w4rkvs/OG-star-tracker-/mechanics/Pcb box/Bottom part of the box.stl

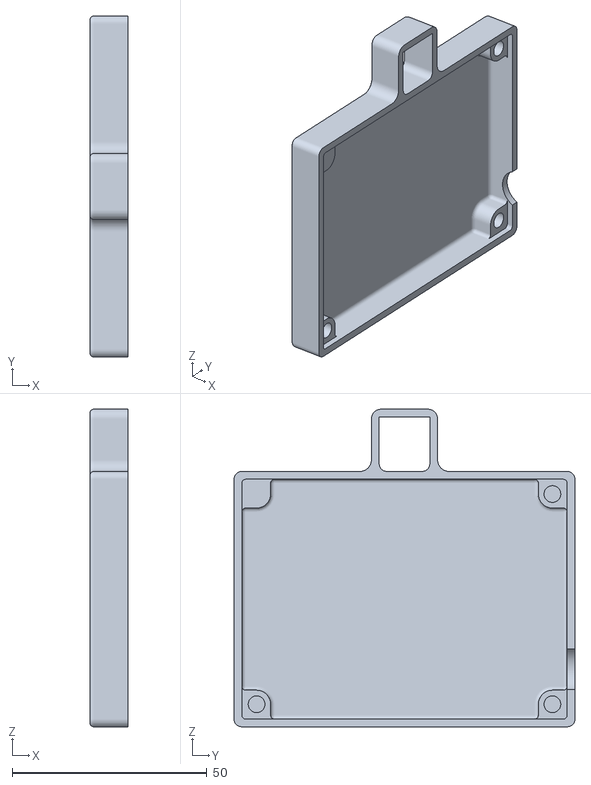
[picture p17: CAD file, 2024-11-18]
mechanics/Pcb box/Bottom part of the box.stl
9.78 x 87.6 x 81.6
