w4rkvs/OG-star-tracker-/mechanics/Test print/test.stl

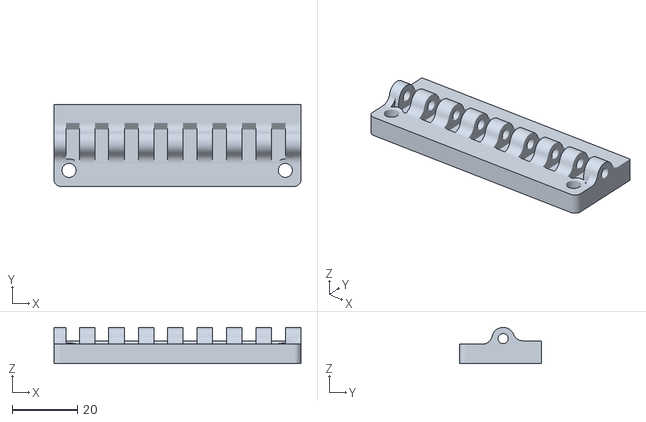
[picture p18: CAD file, 2024-11-18]
mechanics/Test print/test.stl
75.6 x 25.0 x 11.1
