w4rkvs/OG-star-tracker-/mechanics/Top assembly/4 part of geabox.stl

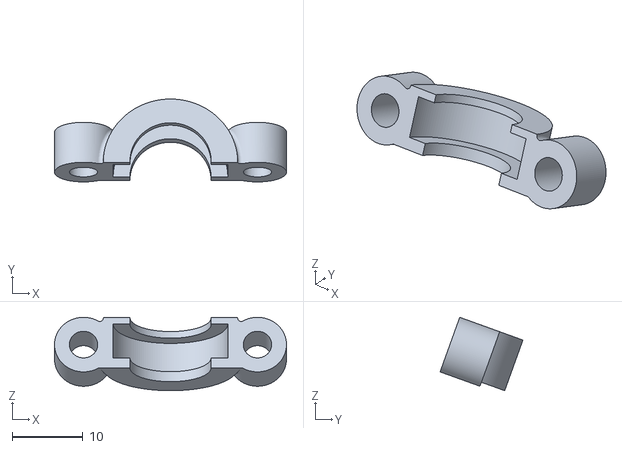
[picture p19: CAD file, 2024-11-18]
mechanics/Top assembly/4 part of geabox.stl
32.8 x 11.7 x 10.4
