w4rkvs/OG-star-tracker-/v1/mechanics/electronic box/top cover.stl

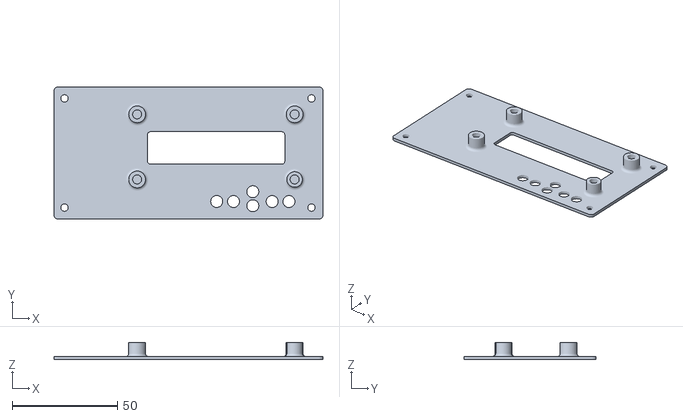
[picture p20: CAD file, 2024-11-18]
v1/mechanics/electronic box/top cover.stl
128.1 x 63.0 x 8.20
