w4rkvs/OG-star-tracker-/v1/mechanics/top asembly/tightener 2x.stl

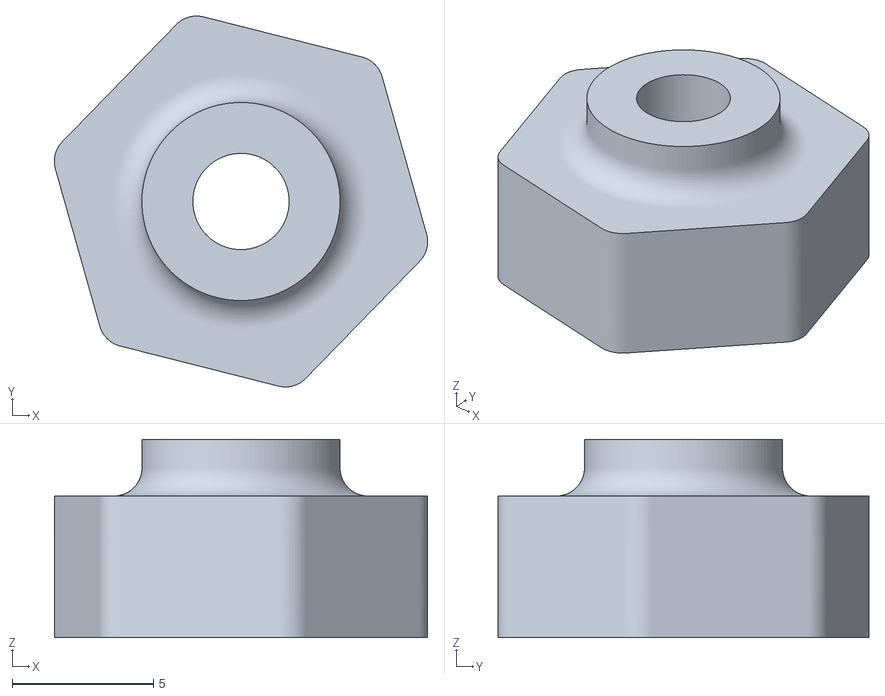
[picture p21: CAD file, 2024-11-18]
v1/mechanics/top asembly/tightener 2x.stl
13.2 x 13.1 x 7.00
