w4rkvs/OG-star-tracker-/v1/mechanics/you also need to print this/bottom holder 2x!.stl

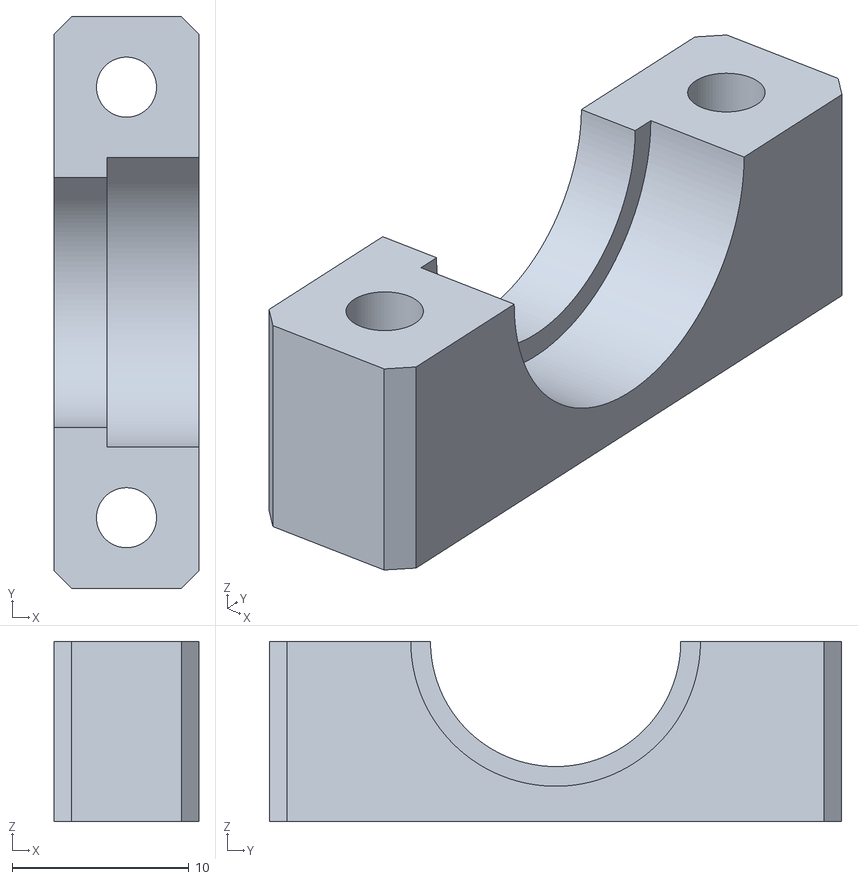
[picture p22: CAD file, 2024-11-18]
v1/mechanics/you also need to print this/bottom holder 2x!.stl
8.20 x 32.4 x 10.2
