w4rkvs/OG-star-tracker-/mechanics/arduino box/box.stl

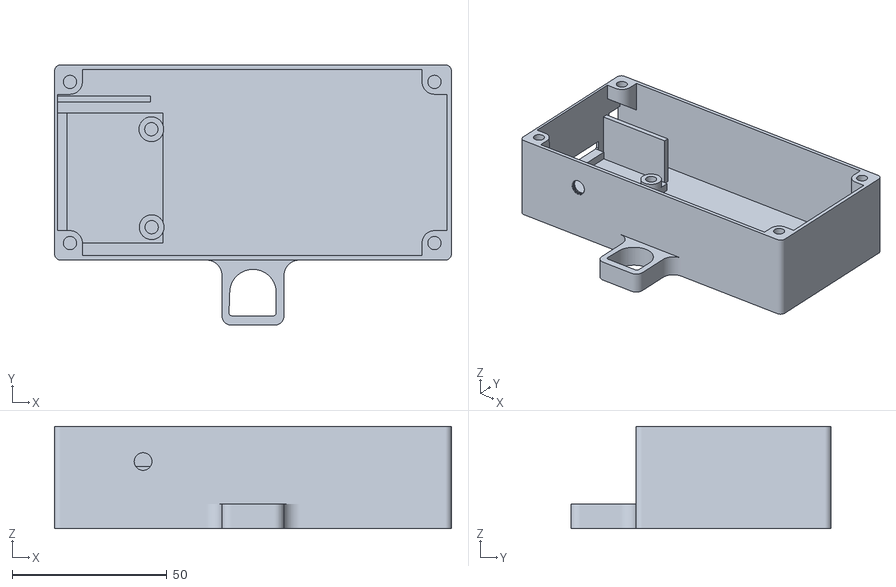
[picture p23: CAD file, 2024-11-18]
mechanics/arduino box/box.stl
128.1 x 84.0 x 33.0
