w4rkvs/OG-star-tracker-/mechanics/DEC upgrade RADEK/bottom-counterweight.stl

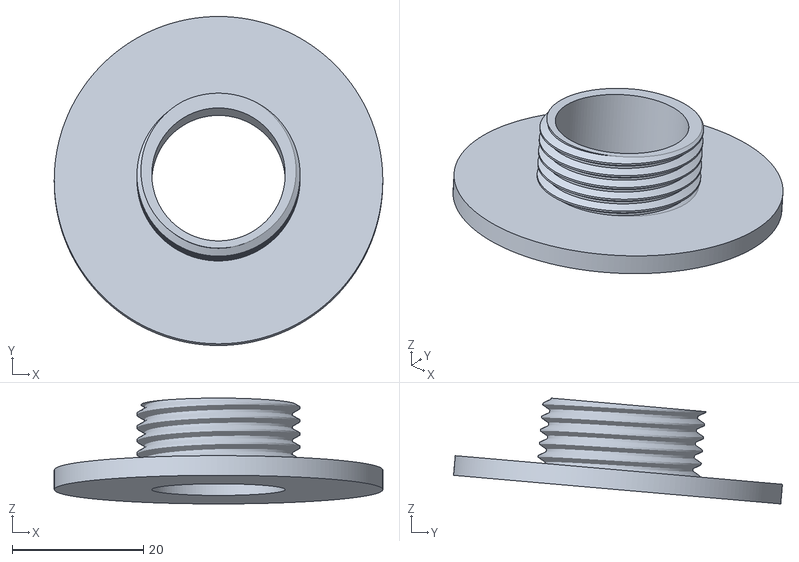
[picture p24: CAD file, 2024-11-18]
mechanics/DEC upgrade RADEK/bottom-counterweight.stl
50.0 x 50.1 x 16.1
