w4rkvs/OG-star-tracker-/mechanics/Knobs and rest of the things/cover for rotating bearing holder.stl

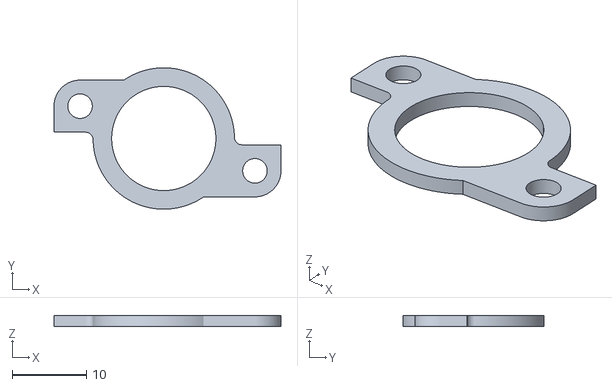
[picture p25: CAD file, 2024-11-18]
mechanics/Knobs and rest of the things/cover for rotating bearing holder.stl
30.5 x 19.0 x 1.50
