w4rkvs/OG-star-tracker-/mechanics/Pcb box/top part.stl

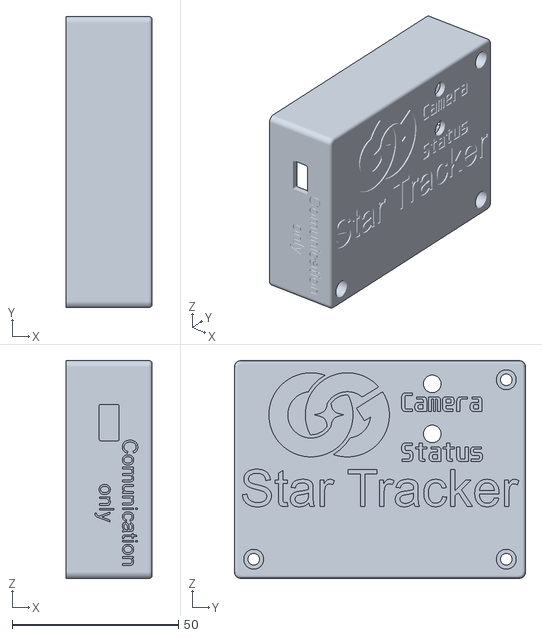
[picture p26: CAD file, 2024-11-18]
mechanics/Pcb box/top part.stl
26.0 x 87.6 x 65.6
