w4rkvs/OG-star-tracker-/mechanics/Test print/test 2.stl

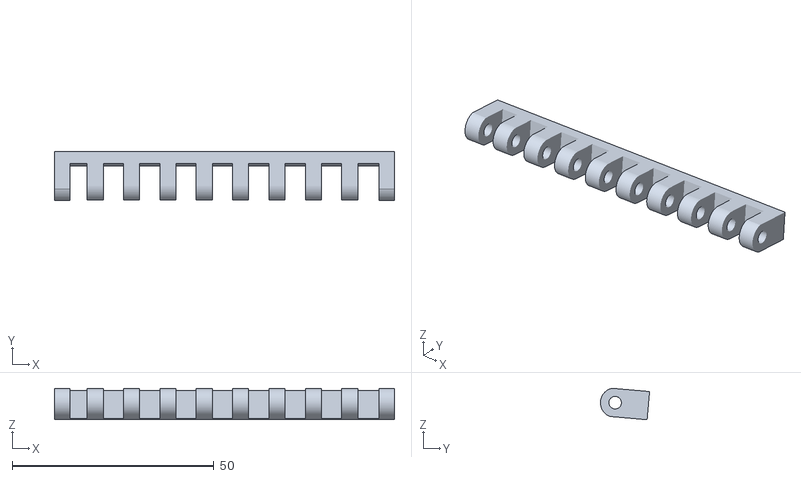
[picture p27: CAD file, 2024-11-18]
mechanics/Test print/test 2.stl
84.2 x 12.2 x 7.79
