w4rkvs/OG-star-tracker-/mechanics/Top assembly/Camera holder m6.stl

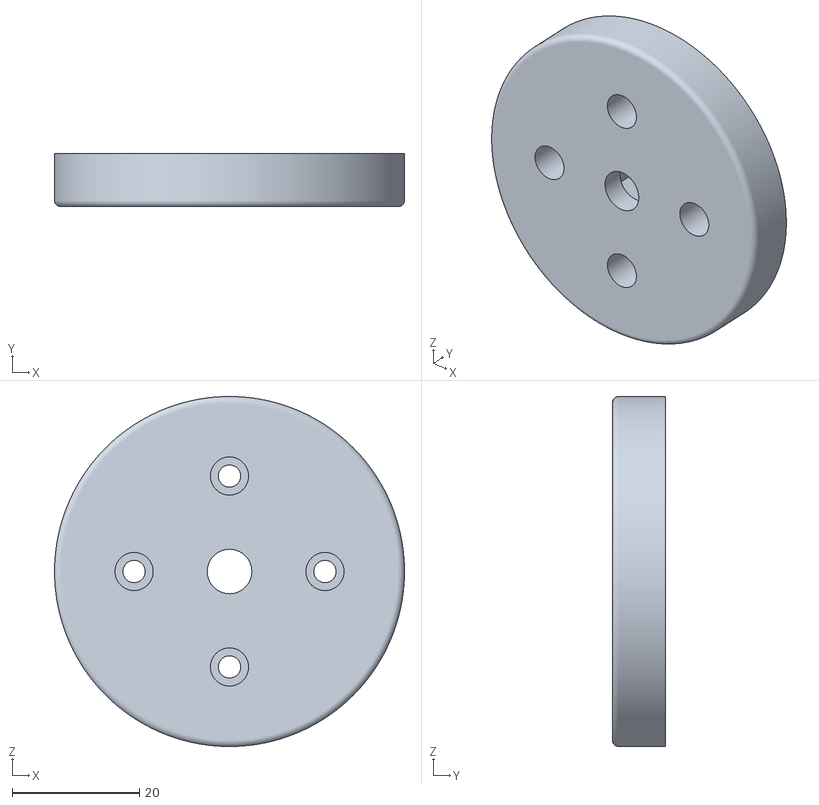
[picture p28: CAD file, 2024-11-18]
mechanics/Top assembly/Camera holder m6.stl
55.0 x 8.40 x 55.0
