w4rkvs/OG-star-tracker-/v1/mechanics/bottom asembly/m5 holder right.stl

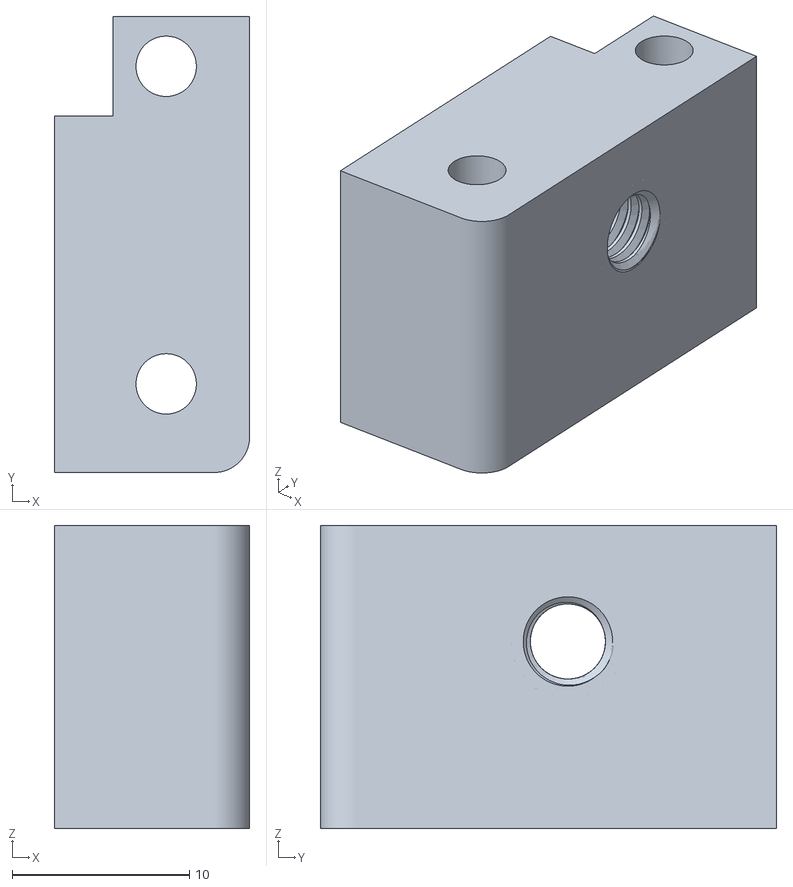
[picture p29: CAD file, 2024-11-18]
v1/mechanics/bottom asembly/m5 holder right.stl
11.0 x 25.7 x 17.1
