w4rkvs/OG-star-tracker-/v1/mechanics/top asembly/gearbox part 2.stl

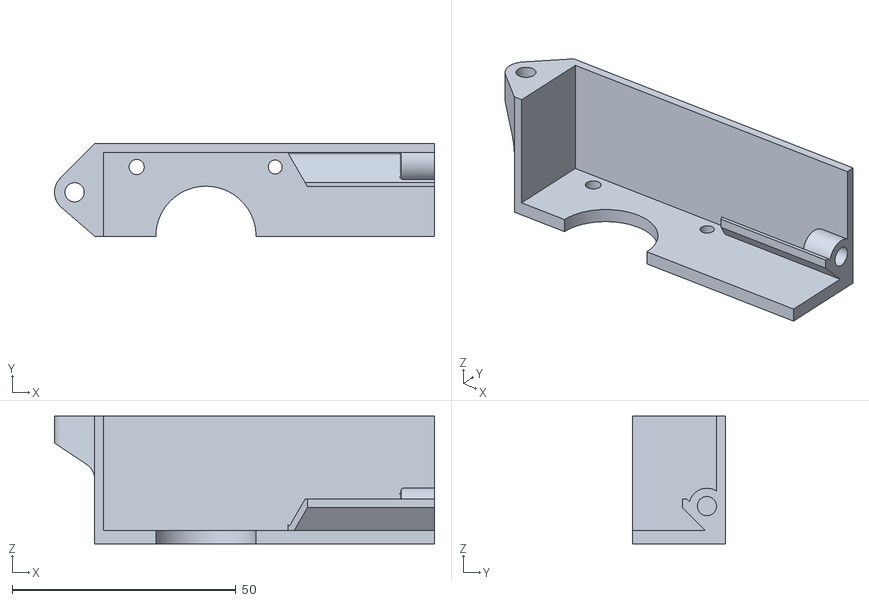
[picture p30: CAD file, 2024-11-18]
v1/mechanics/top asembly/gearbox part 2.stl
85.0 x 20.7 x 28.5
