w4rkvs/OG-star-tracker-/v1/mechanics/you also need to print this/bottom wedge holder 2x!.stl

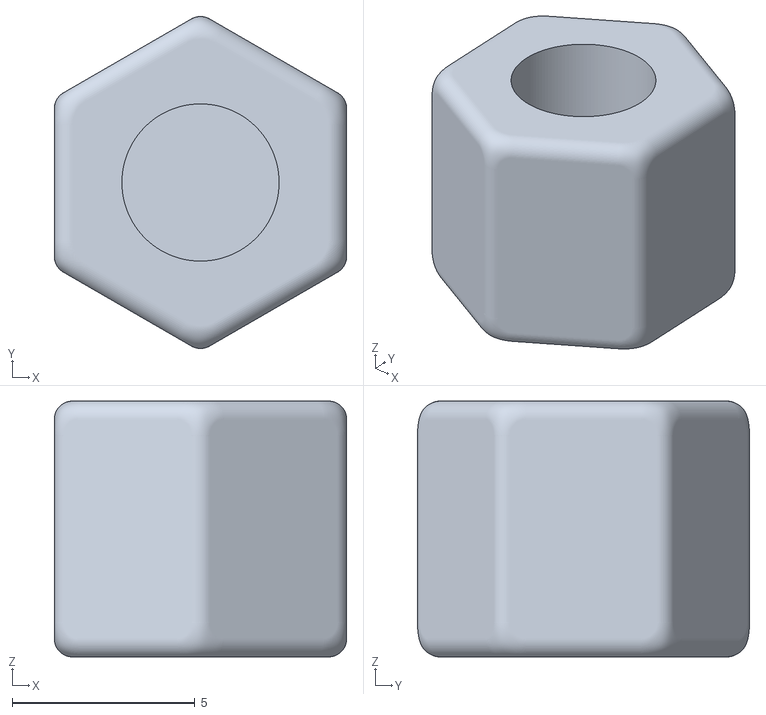
[picture p31: CAD file, 2024-11-18]
v1/mechanics/you also need to print this/bottom wedge holder 2x!.stl
8.00 x 9.08 x 7.00
