w4rkvs/OG-star-tracker-/mechanics/DEC upgrade RADEK/top-counterweight.stl

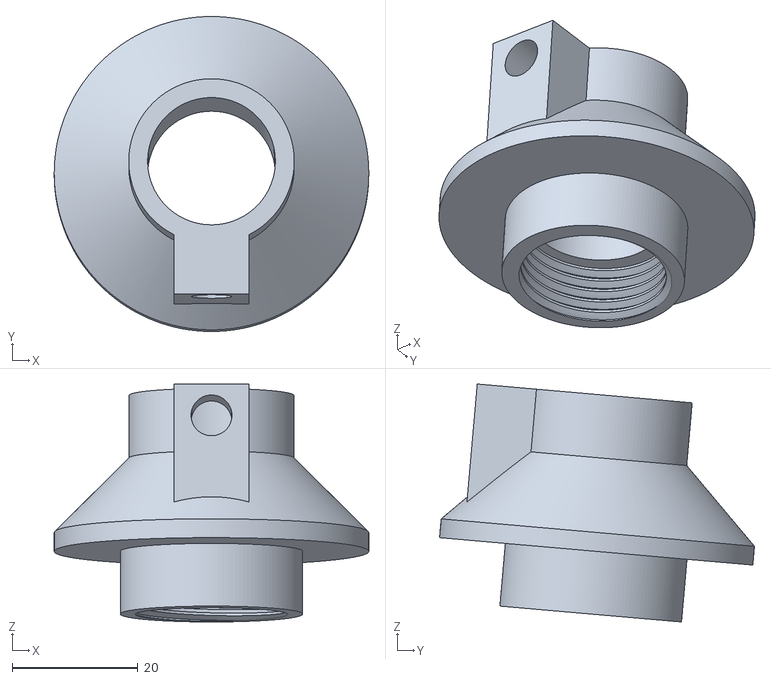
[picture p32: CAD file, 2024-11-18]
mechanics/DEC upgrade RADEK/top-counterweight.stl
50.0 x 50.1 x 37.8
