w4rkvs/OG-star-tracker-/mechanics/Knobs and rest of the things/bottom part with m5 threaded insert.stl

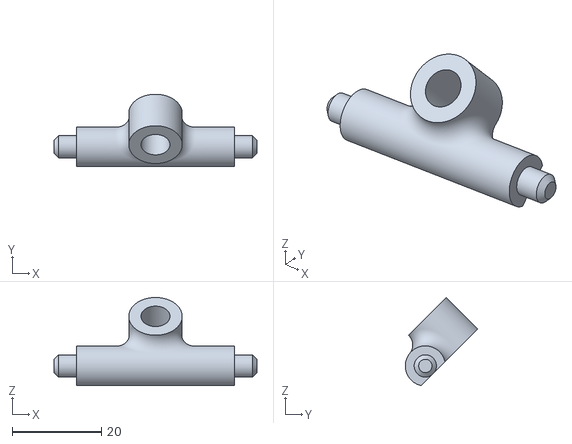
[picture p33: CAD file, 2024-11-18]
mechanics/Knobs and rest of the things/bottom part with m5 threaded insert.stl
45.6 x 16.3 x 19.8
