w4rkvs/OG-star-tracker-/mechanics/Top assembly/slider.stl

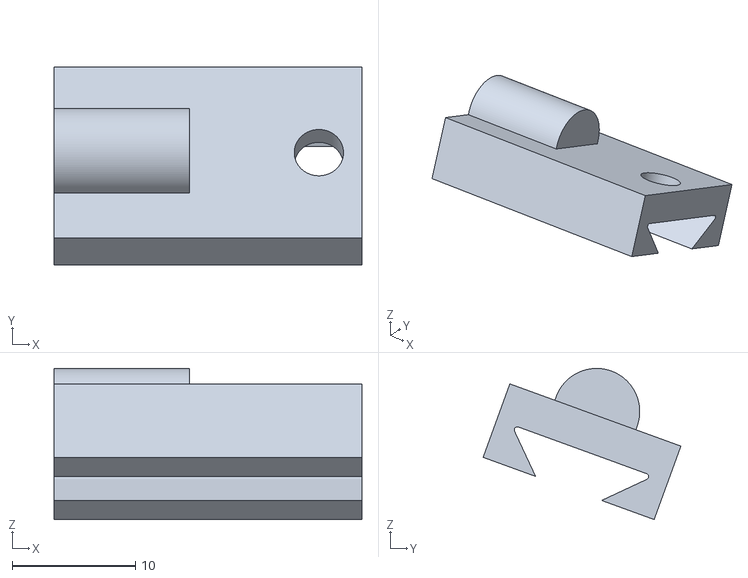
[picture p34: CAD file, 2024-11-18]
mechanics/Top assembly/slider.stl
25.0 x 16.1 x 12.3
