w4rkvs/OG-star-tracker-/v1/mechanics/electronic box/button.stl

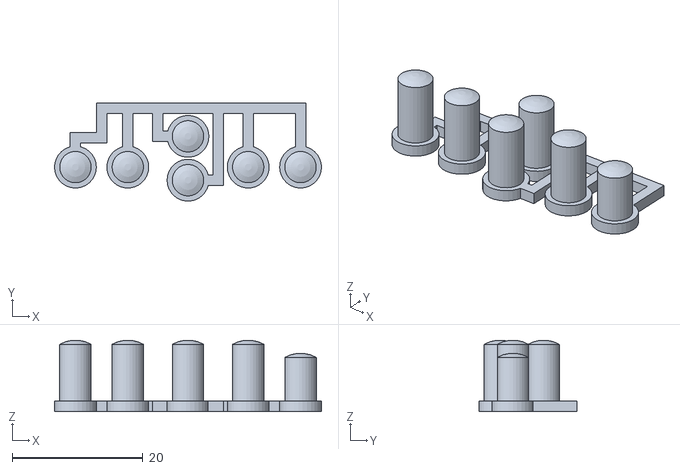
[picture p35: CAD file, 2024-11-18]
v1/mechanics/electronic box/button.stl
40.8 x 15.0 x 10.9
