w4rkvs/OG-star-tracker-/v1/mechanics/top asembly/gearbox part 1.stl

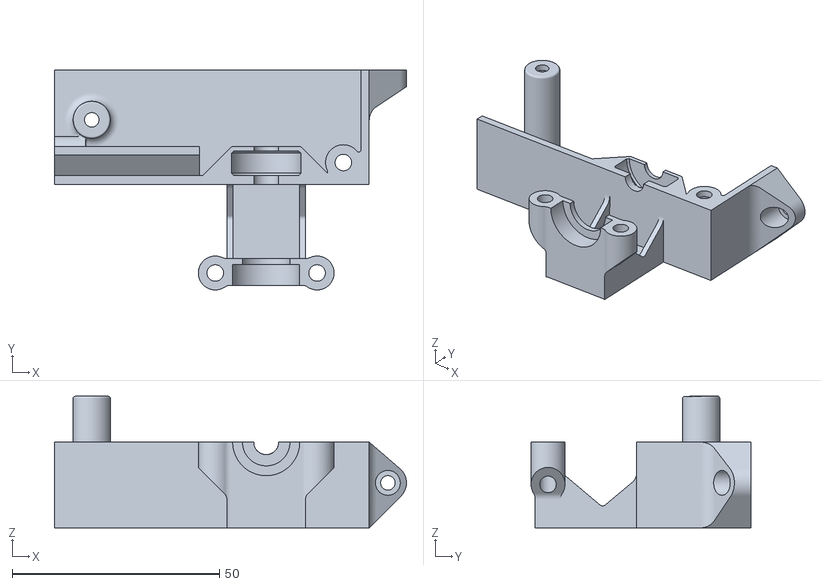
[picture p36: CAD file, 2024-11-18]
v1/mechanics/top asembly/gearbox part 1.stl
85.0 x 53.1 x 31.8
