w4rkvs/OG-star-tracker-/v1/mechanics/you also need to print this/rotator with thread.stl

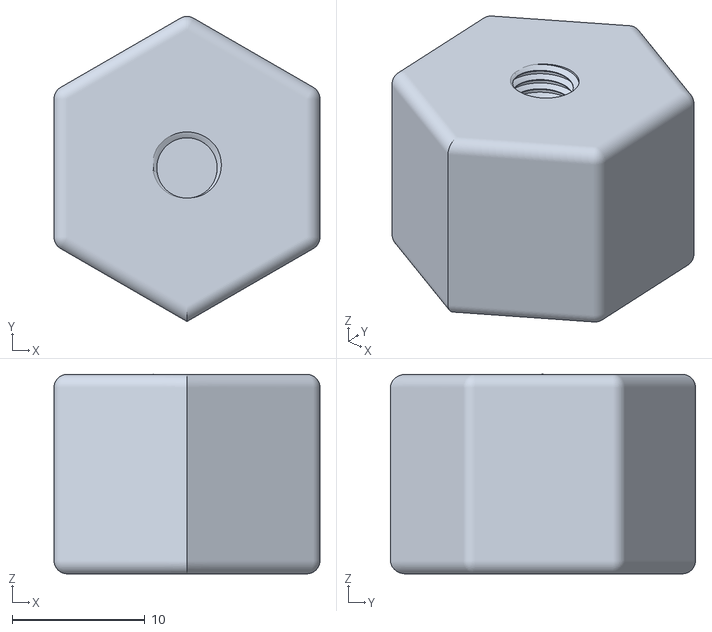
[picture p37: CAD file, 2024-11-18]
v1/mechanics/you also need to print this/rotator with thread.stl
20.0 x 22.9 x 15.0
