w4rkvs/OG-star-tracker-/mechanics/Bottom assembly/Stationary part with m5 threaded inser and 3 8 threaded insert.stl

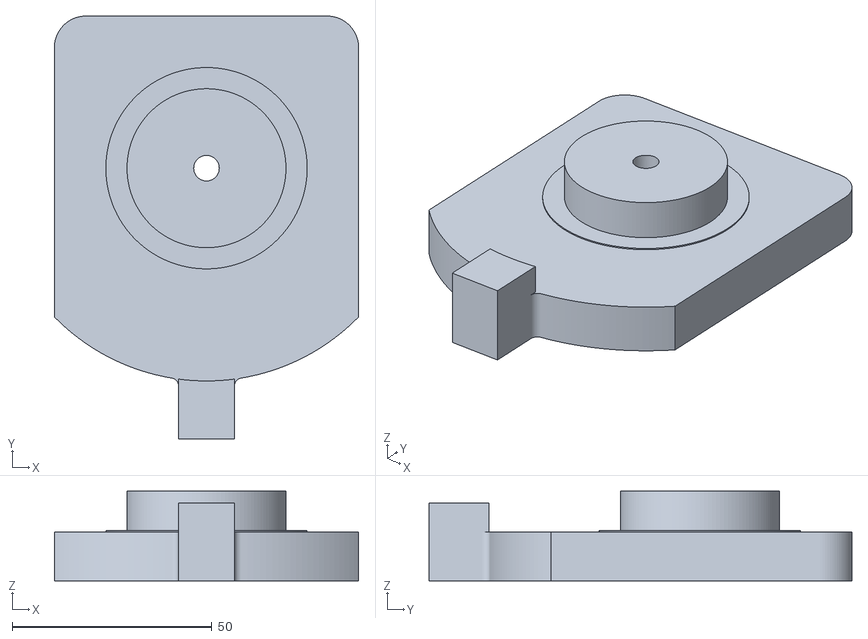
[picture p38: CAD file, 2024-11-18]
mechanics/Bottom assembly/Stationary part with m5 threaded inser and 3 8 threaded insert.stl
76.2 x 105.9 x 22.5
