w4rkvs/OG-star-tracker-/mechanics/DEC upgrade RADEK/bearing-holder.stl

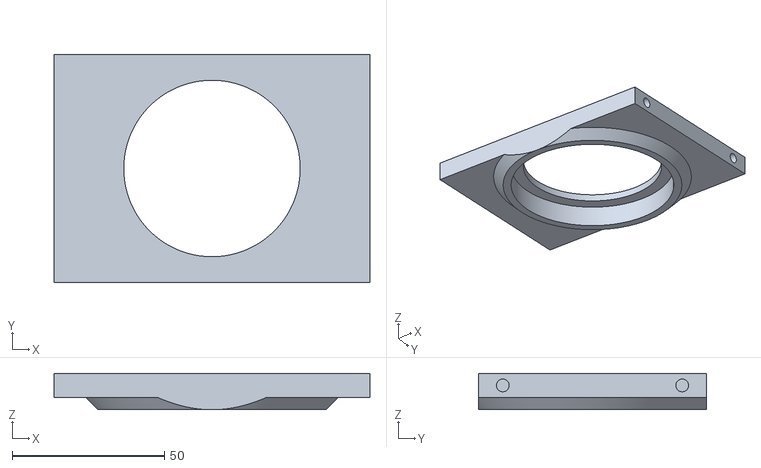
[picture p39: CAD file, 2024-11-18]
mechanics/DEC upgrade RADEK/bearing-holder.stl
103.9 x 75.0 x 12.0
