w4rkvs/OG-star-tracker-/mechanics/Knobs and rest of the things/knob for laser.stl

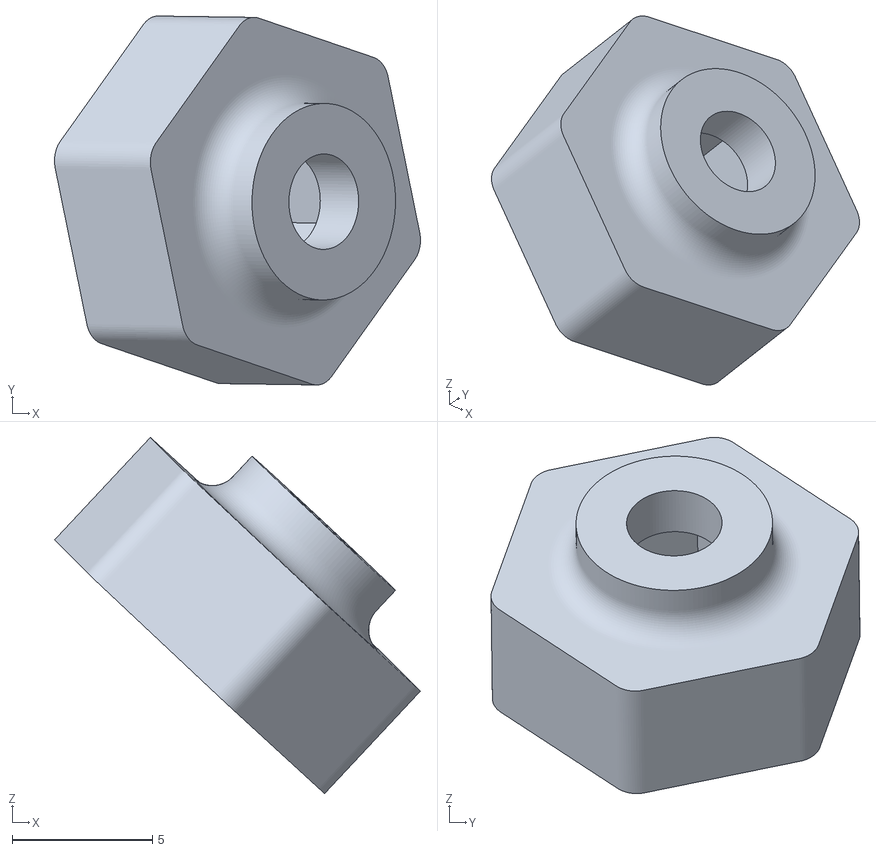
[picture p40: CAD file, 2024-11-18]
mechanics/Knobs and rest of the things/knob for laser.stl
13.0 x 13.1 x 12.7
