w4rkvs/OG-star-tracker-/mechanics/Top assembly/Camera holder 1 4-20.stl

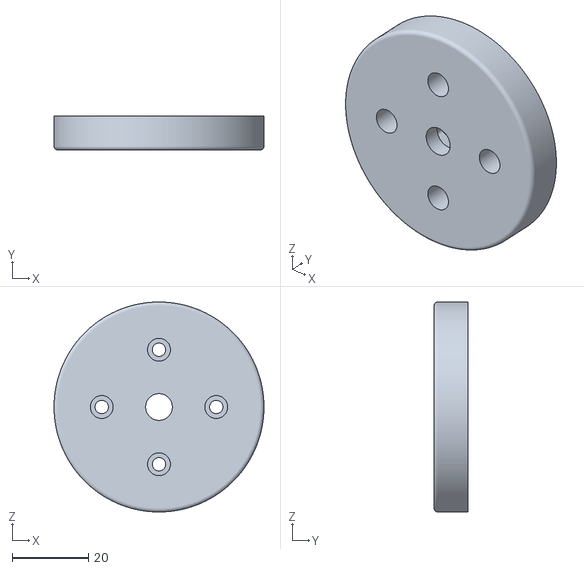
[picture p41: CAD file, 2024-11-18]
mechanics/Top assembly/Camera holder 1 4-20.stl
55.0 x 8.90 x 55.0
