w4rkvs/OG-star-tracker-/v1/mechanics/bottom asembly/m5 holder left.stl

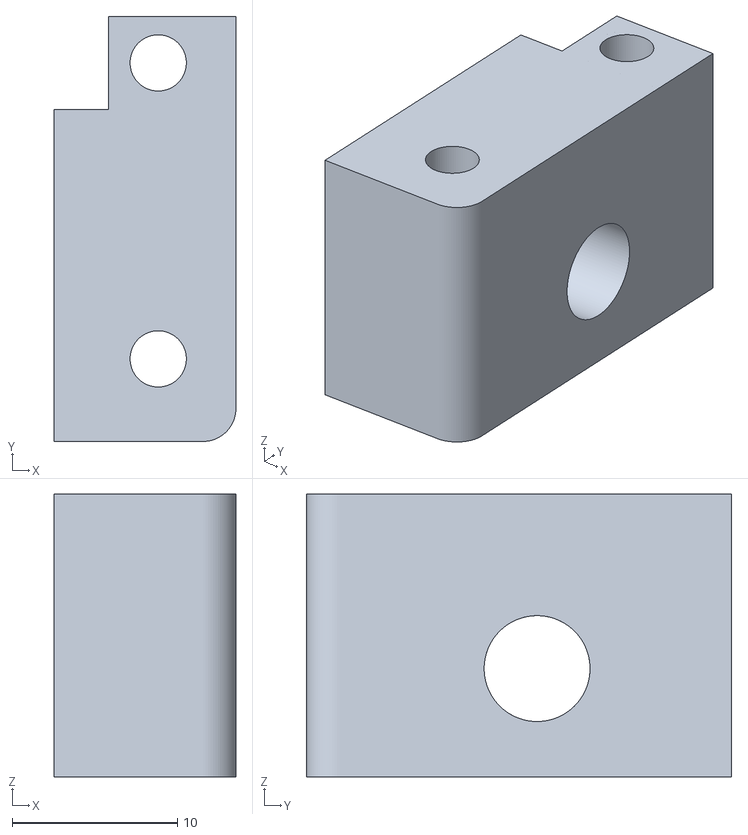
[picture p42: CAD file, 2024-11-18]
v1/mechanics/bottom asembly/m5 holder left.stl
11.0 x 25.7 x 17.1
