w4rkvs/OG-star-tracker-/v1/mechanics/top asembly/between part.stl

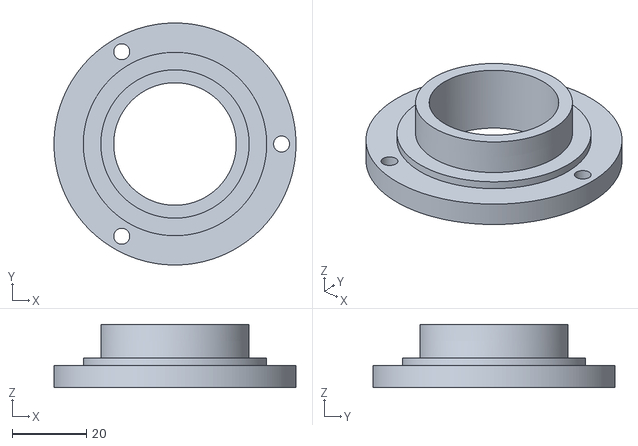
[picture p43: CAD file, 2024-11-18]
v1/mechanics/top asembly/between part.stl
65.2 x 65.2 x 17.0
