w4rkvs/OG-star-tracker-/mechanics/Knobs and rest of the things/rotating bearing holder.stl

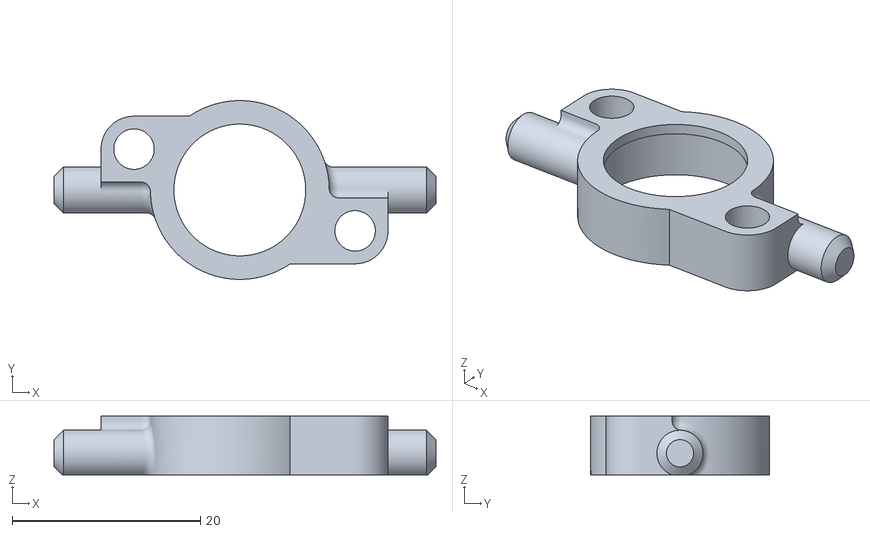
[picture p44: CAD file, 2024-11-18]
mechanics/Knobs and rest of the things/rotating bearing holder.stl
40.6 x 19.0 x 6.25
