w4rkvs/OG-star-tracker-/mechanics/Top assembly/Cover and tightener.stl

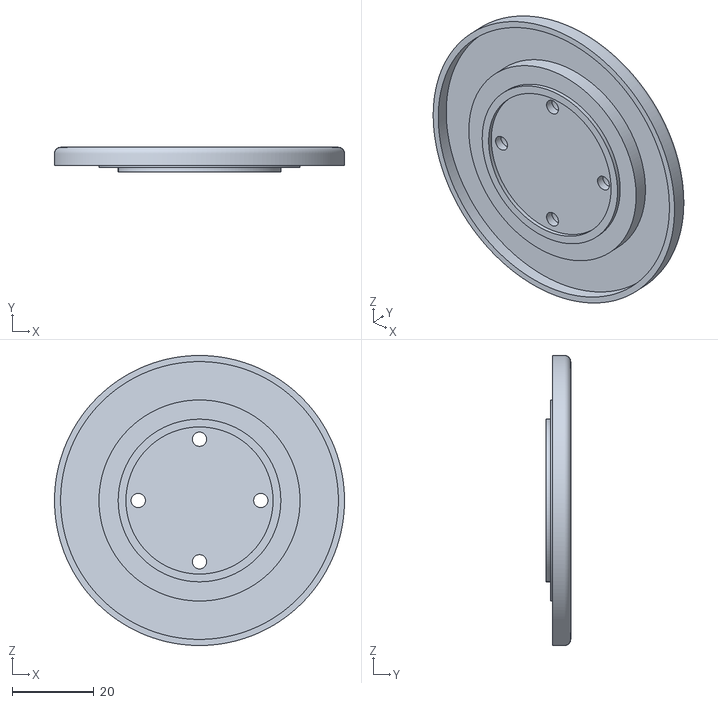
[picture p45: CAD file, 2024-11-18]
mechanics/Top assembly/Cover and tightener.stl
71.0 x 6.00 x 71.0
