w4rkvs/OG-star-tracker-/v1/mechanics/bottom asembly/middle bearing holder.stl

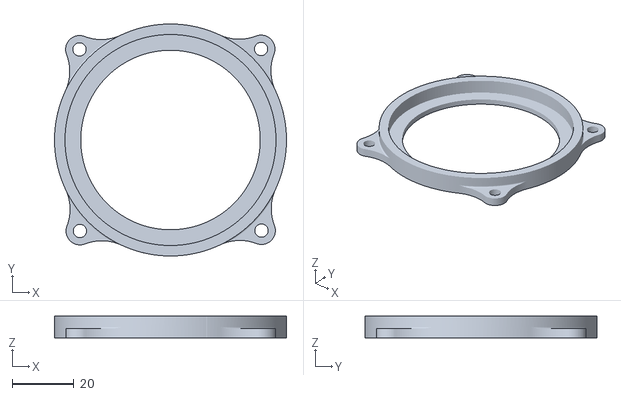
[picture p46: CAD file, 2024-11-18]
v1/mechanics/bottom asembly/middle bearing holder.stl
75.0 x 75.0 x 7.00
