w4rkvs/OG-star-tracker-/v1/mechanics/top asembly/gearbox part 3.stl

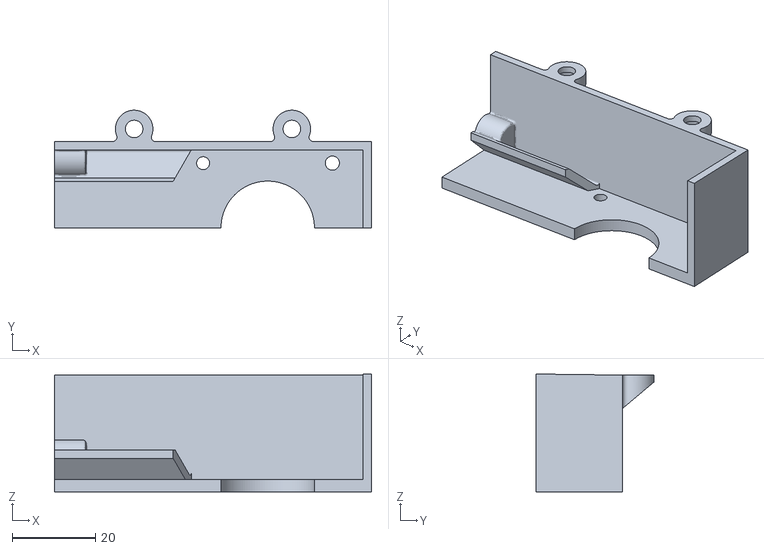
[picture p47: CAD file, 2024-11-18]
v1/mechanics/top asembly/gearbox part 3.stl
76.0 x 28.2 x 28.3
