w4rkvs/OG-star-tracker-/v1/mechanics/you also need to print this/top holder 2x!.stl

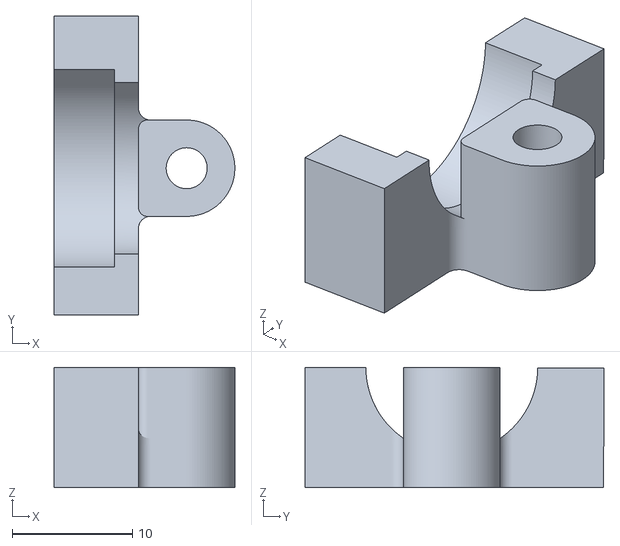
[picture p48: CAD file, 2024-11-18]
v1/mechanics/you also need to print this/top holder 2x!.stl
15.0 x 24.8 x 10.0
