w4rkvs/OG-star-tracker-/mechanics/DEC upgrade RADEK/base.stl

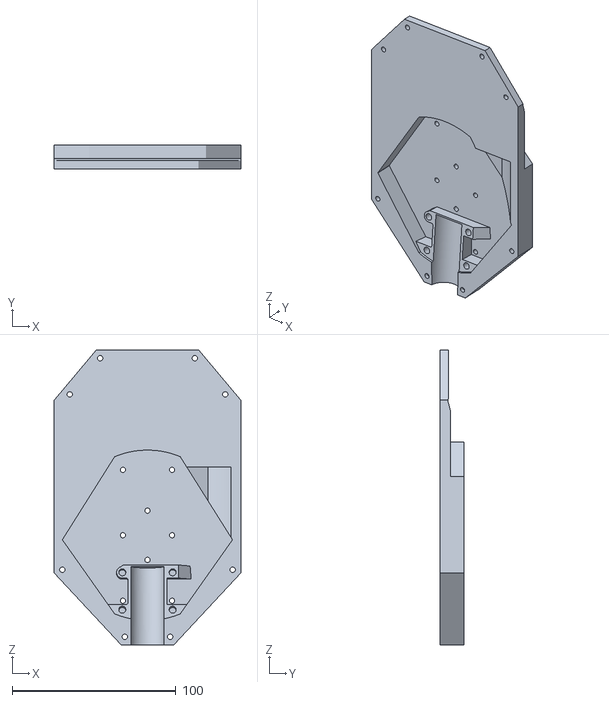
[picture p49: CAD file, 2024-11-18]
mechanics/DEC upgrade RADEK/base.stl
113.9 x 14.4 x 180.0
