w4rkvs/OG-star-tracker-/mechanics/Knobs and rest of the things/Big top knob m3 left.stl

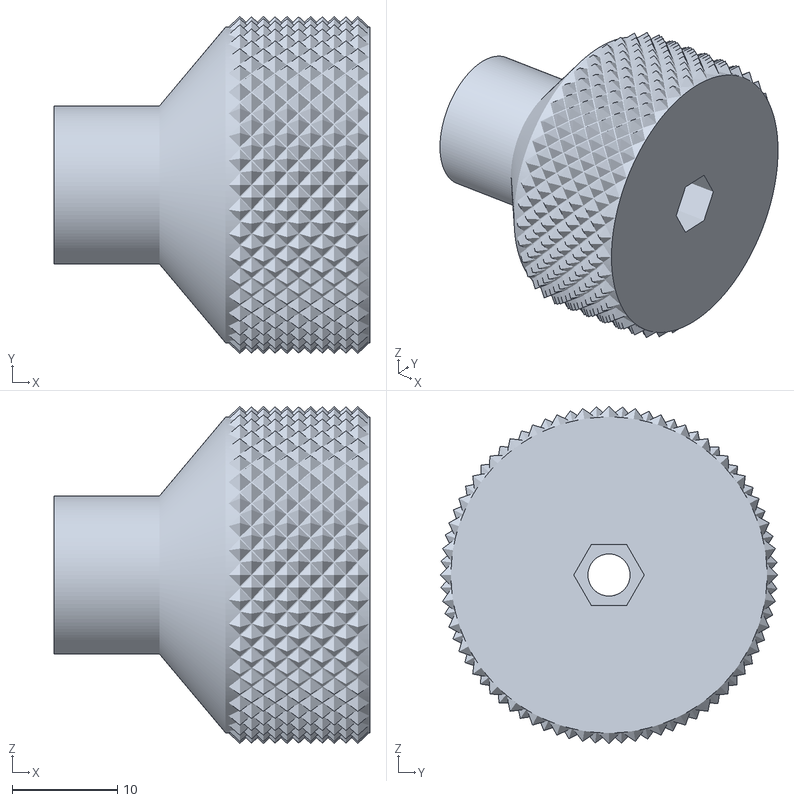
[picture p50: CAD file, 2024-11-18]
mechanics/Knobs and rest of the things/Big top knob m3 left.stl
30.0 x 32.0 x 32.0
