w4rkvs/OG-star-tracker-/mechanics/Top assembly/Camera holder south 1 4-20.stl

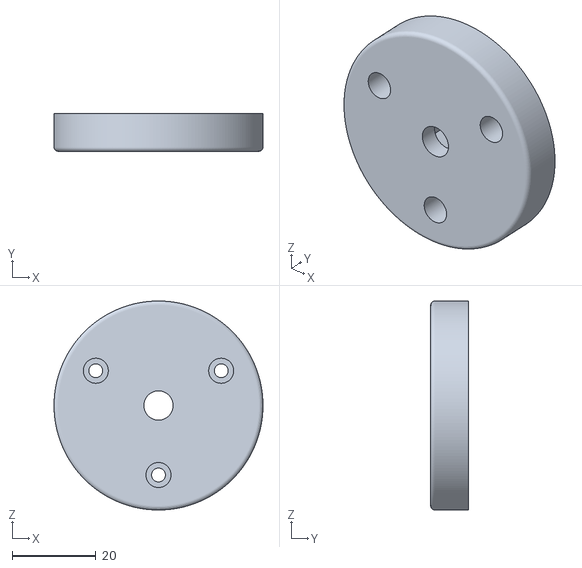
[picture p51: CAD file, 2024-11-18]
mechanics/Top assembly/Camera holder south 1 4-20.stl
50.0 x 9.00 x 50.0
