w4rkvs/OG-star-tracker-/v1/mechanics/bottom asembly/stationary part.stl

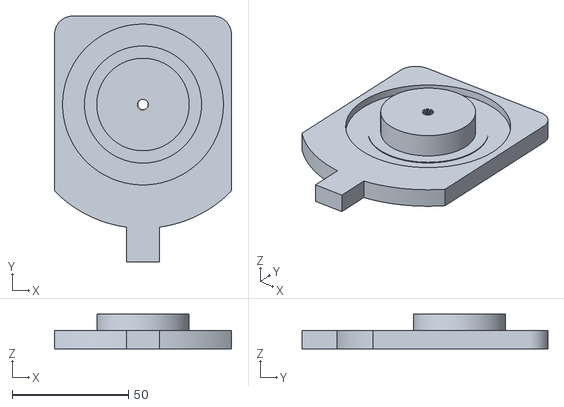
[picture p52: CAD file, 2024-11-18]
v1/mechanics/bottom asembly/stationary part.stl
76.2 x 105.9 x 15.0
