w4rkvs/OG-star-tracker-/v1/mechanics/top asembly/gerbox bearing holder inside.stl

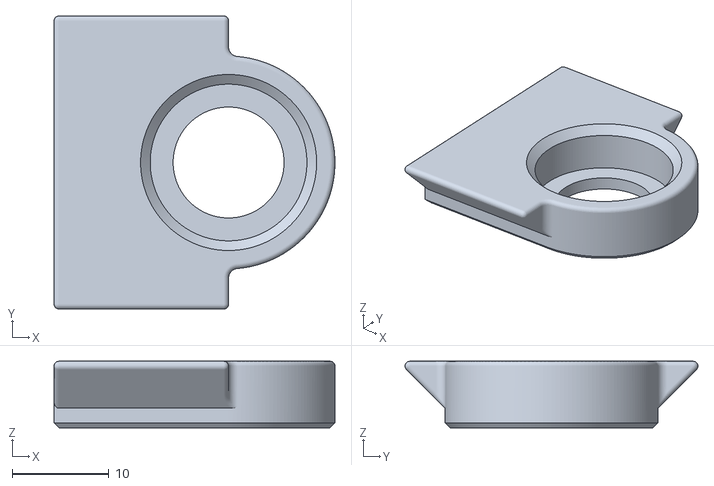
[picture p53: CAD file, 2024-11-18]
v1/mechanics/top asembly/gerbox bearing holder inside.stl
29.1 x 30.3 x 6.88
