w4rkvs/OG-star-tracker-/v1/mechanics/you also need to print this/bottom part with thread.stl

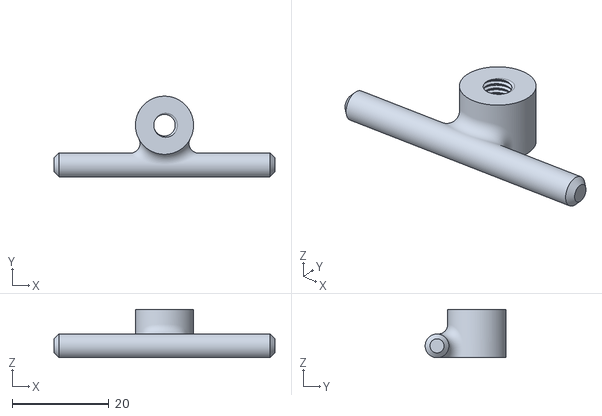
[picture p54: CAD file, 2024-11-18]
v1/mechanics/you also need to print this/bottom part with thread.stl
45.6 x 16.6 x 10.0
