w4rkvs/OG-star-tracker-/mechanics/Bottom assembly/Stationary part all threads are 3d printed.stl

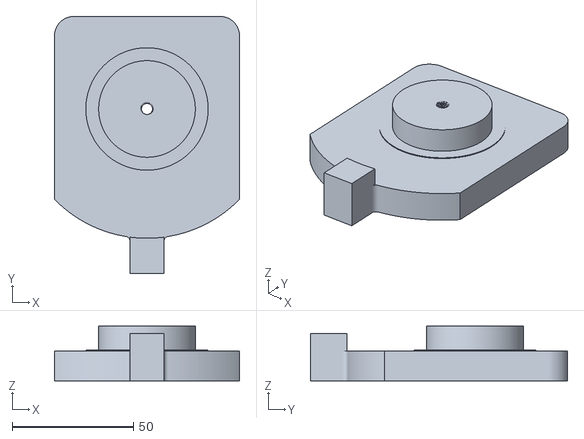
[picture p55: CAD file, 2024-11-18]
mechanics/Bottom assembly/Stationary part all threads are 3d printed.stl
76.2 x 105.9 x 22.5
