w4rkvs/OG-star-tracker-/mechanics/Top assembly/2 part of gearbox.stl

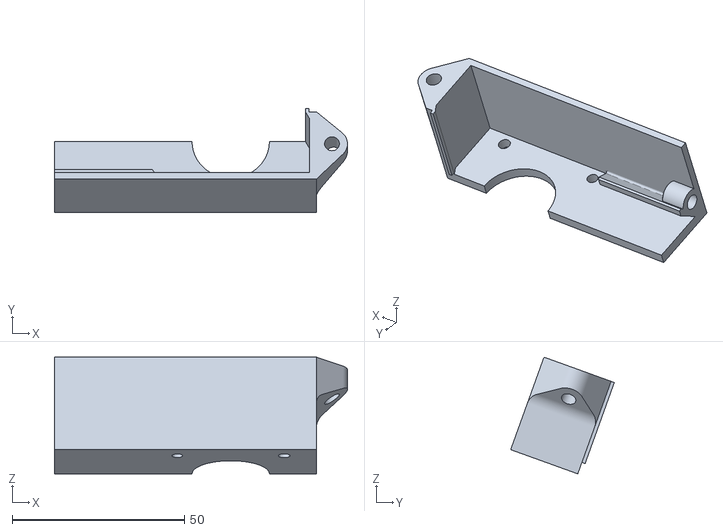
[picture p56: CAD file, 2024-11-18]
mechanics/Top assembly/2 part of gearbox.stl
85.0 x 30.1 x 33.9
