w4rkvs/OG-star-tracker-/v1/mechanics/you also need to print this/rotating bearing holder.stl

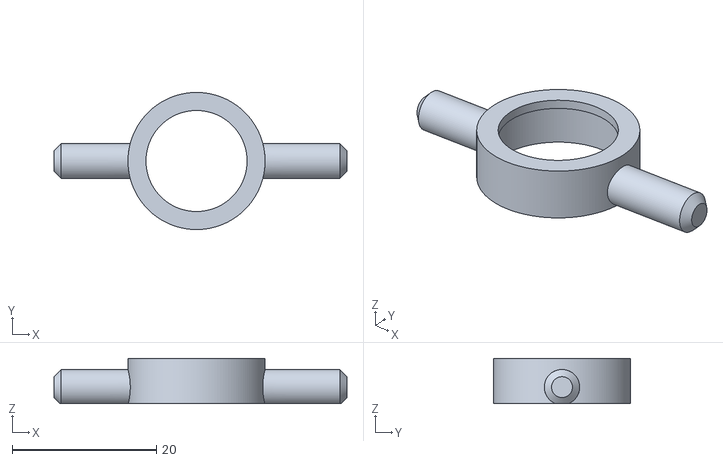
[picture p57: CAD file, 2024-11-18]
v1/mechanics/you also need to print this/rotating bearing holder.stl
40.6 x 19.0 x 6.30
