w4rkvs/OG-star-tracker-/mechanics/Bottom assembly/Stationary part for surveyors tripod with m5 threaded insert.stl

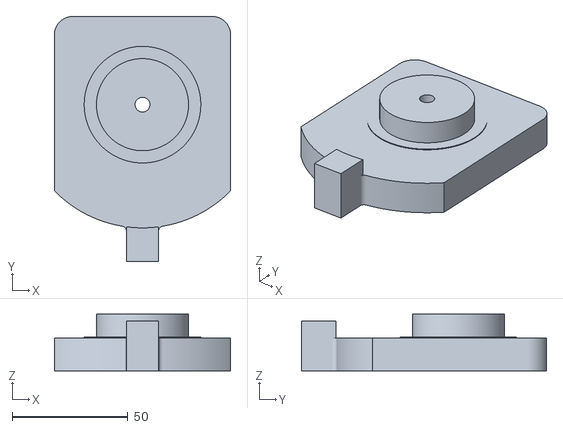
[picture p58: CAD file, 2024-11-18]
mechanics/Bottom assembly/Stationary part for surveyors tripod with m5 threaded insert.stl
76.2 x 105.9 x 24.5
