w4rkvs/OG-star-tracker-/mechanics/DEC upgrade RADEK/rod-tightener.stl

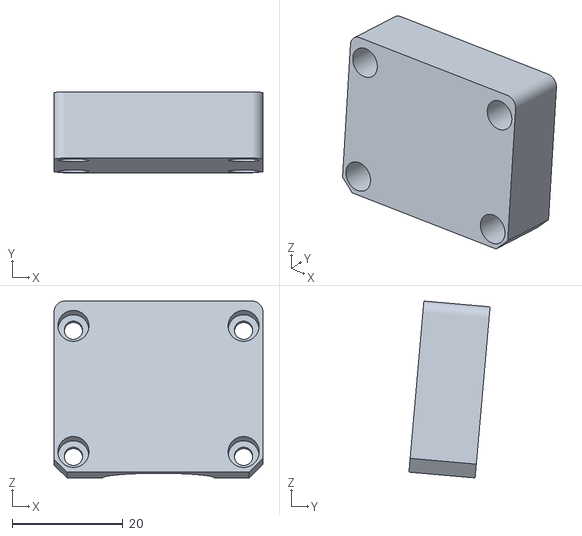
[picture p59: CAD file, 2024-11-18]
mechanics/DEC upgrade RADEK/rod-tightener.stl
37.7 x 14.7 x 31.9
