w4rkvs/OG-star-tracker-/mechanics/Knobs and rest of the things/top holder print 2x !.stl

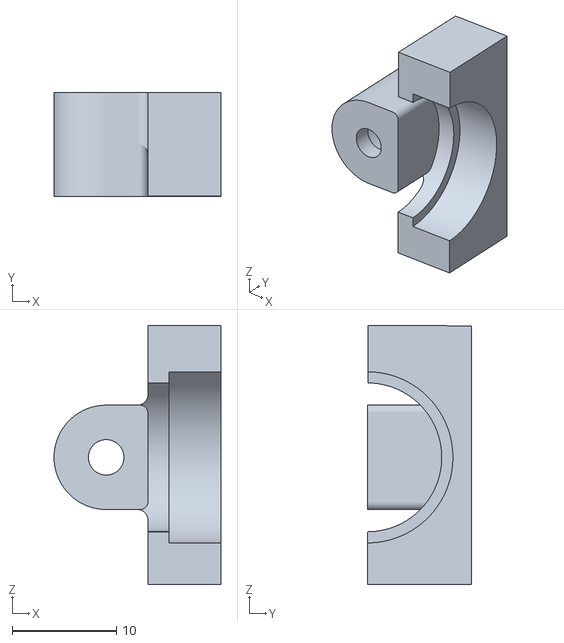
[picture p60: CAD file, 2024-11-18]
mechanics/Knobs and rest of the things/top holder print 2x !.stl
16.0 x 10.0 x 24.8
