w4rkvs/OG-star-tracker-/mechanics/Top assembly/1 part of gearboox.stl

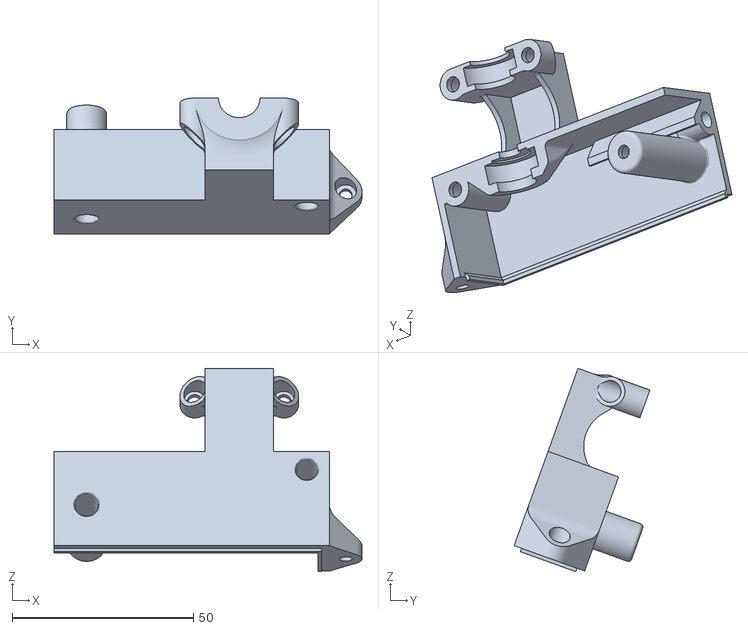
[picture p61: CAD file, 2024-11-18]
mechanics/Top assembly/1 part of gearboox.stl
85.0 x 37.5 x 56.1
