w4rkvs/OG-star-tracker-/v1/mechanics/top asembly/door.stl

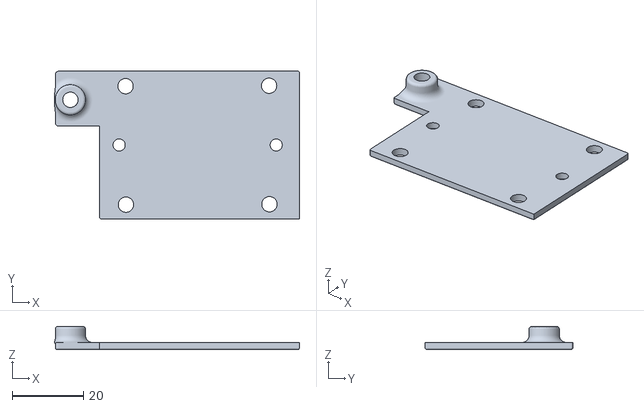
[picture p62: CAD file, 2024-11-18]
v1/mechanics/top asembly/door.stl
68.6 x 41.4 x 6.50
