w4rkvs/OG-star-tracker-/v1/mechanics/you also need to print this/bottom part with m5 threaded insert.stl

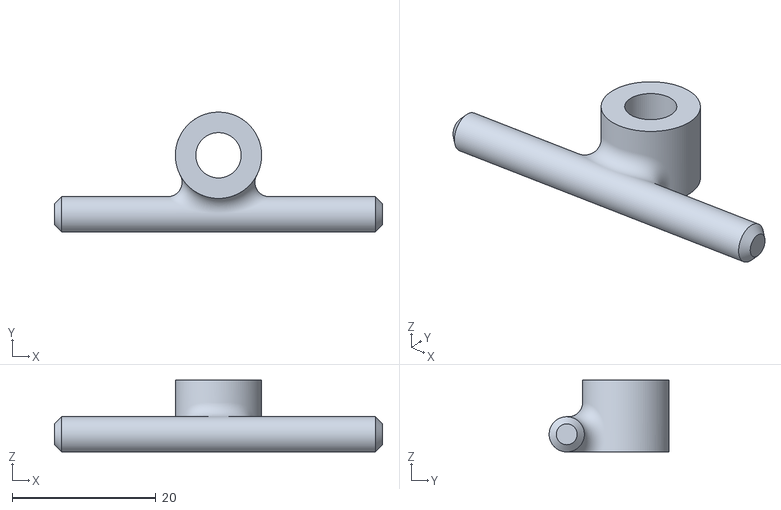
[picture p63: CAD file, 2024-11-18]
v1/mechanics/you also need to print this/bottom part with m5 threaded insert.stl
45.6 x 16.6 x 10.0
