w4rkvs/OG-star-tracker-/mechanics/DEC upgrade RADEK/dec-2-part-of-gearbox-rj45.stl

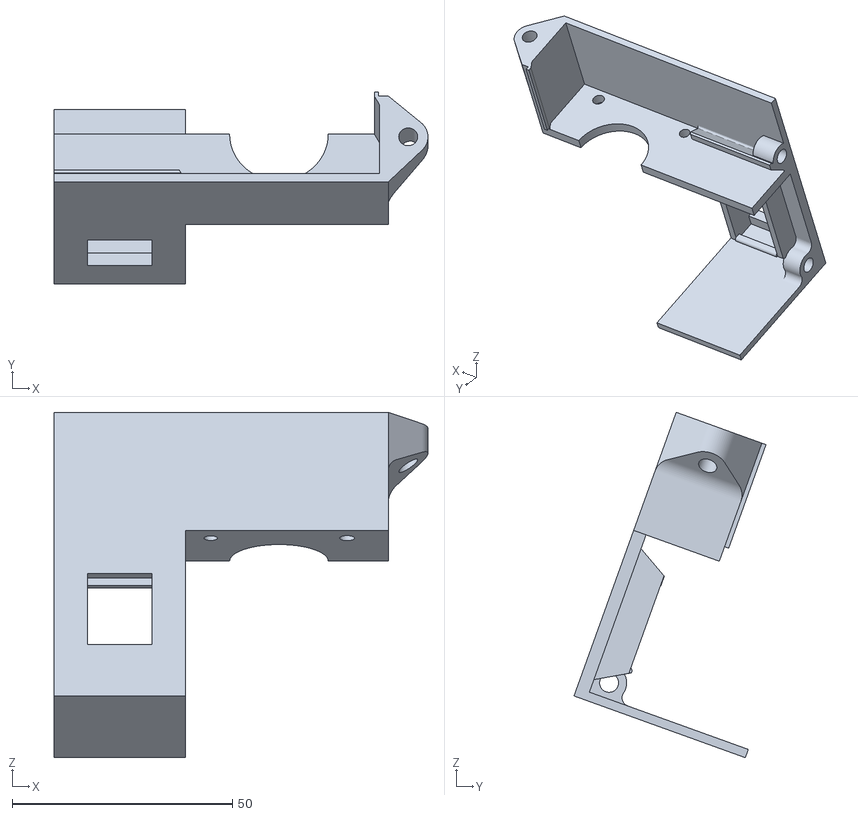
[picture p64: CAD file, 2024-11-18]
mechanics/DEC upgrade RADEK/dec-2-part-of-gearbox-rj45.stl
85.0 x 43.6 x 78.5
