w4rkvs/OG-star-tracker-/mechanics/Knobs and rest of the things/m5 bottom knob print 2x !.stl

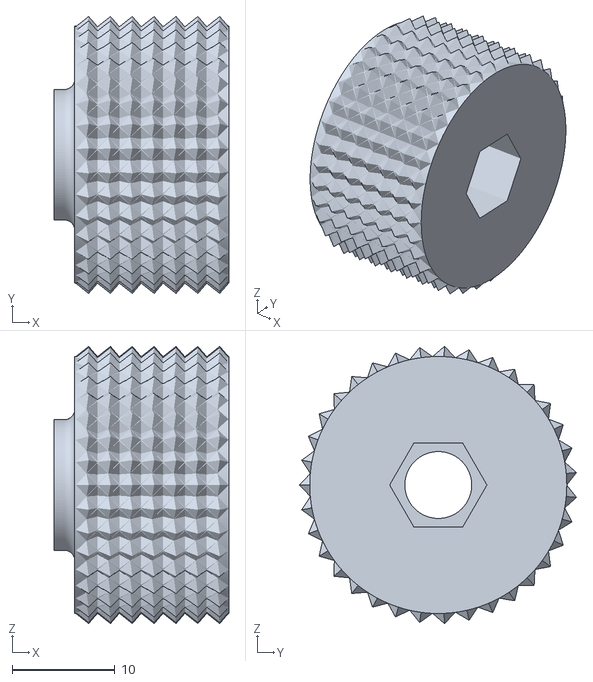
[picture p65: CAD file, 2024-11-18]
mechanics/Knobs and rest of the things/m5 bottom knob print 2x !.stl
17.0 x 26.9 x 27.0
