w4rkvs/OG-star-tracker-/mechanics/Top assembly/door.stl

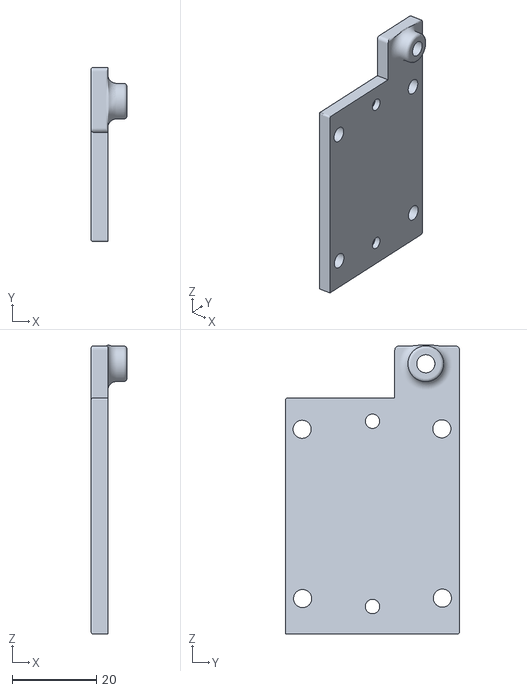
[picture p66: CAD file, 2024-11-18]
mechanics/Top assembly/door.stl
8.50 x 41.4 x 68.6
