w4rkvs/OG-star-tracker-/v1/mechanics/top asembly/attachment for slider.stl

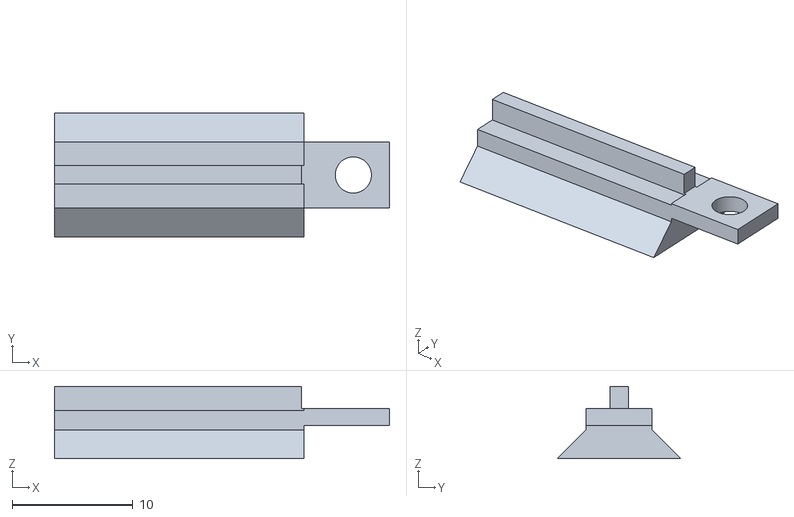
[picture p67: CAD file, 2024-11-18]
v1/mechanics/top asembly/attachment for slider.stl
27.8 x 10.3 x 6.01
