w4rkvs/OG-star-tracker-/mechanics/DEC upgrade RADEK/DEC_Arca_clamp_moving.stl

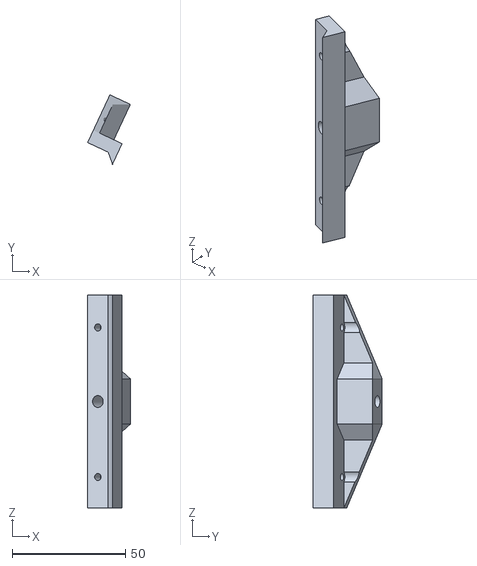
[picture p68: CAD file, 2024-11-18]
mechanics/DEC upgrade RADEK/DEC_Arca_clamp_moving.stl
18.9 x 30.6 x 94.0
