w4rkvs/OG-star-tracker-/mechanics/Knobs and rest of the things/bottom part with m5 thread.stl

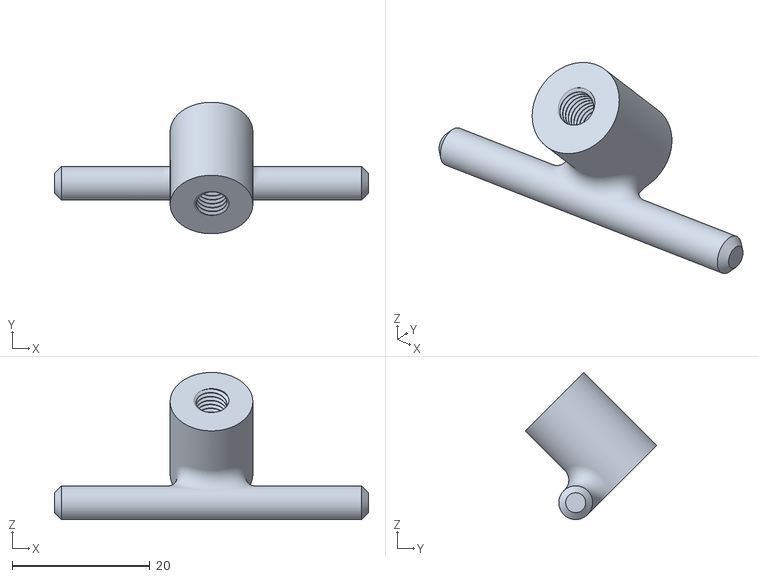
[picture p69: CAD file, 2024-11-18]
mechanics/Knobs and rest of the things/bottom part with m5 thread.stl
45.6 x 19.1 x 21.4
