w4rkvs/OG-star-tracker-/v1/mechanics/top asembly/slider.stl

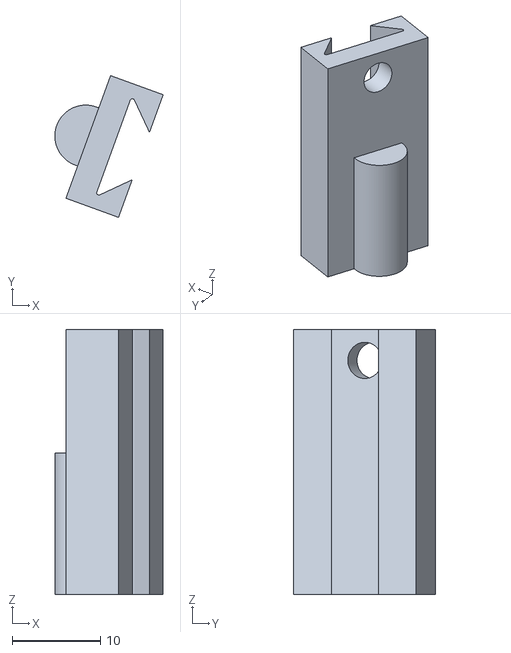
[picture p70: CAD file, 2024-11-18]
v1/mechanics/top asembly/slider.stl
12.3 x 16.1 x 30.0
