w4rkvs/OG-star-tracker-/mechanics/DEC upgrade RADEK/DEC_Arca_clamp_tightener.stl

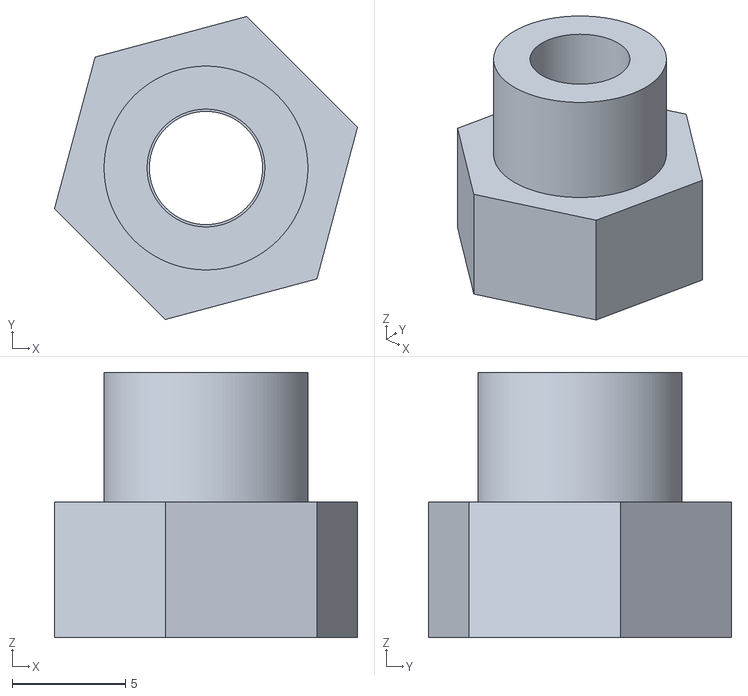
[picture p71: CAD file, 2024-11-18]
mechanics/DEC upgrade RADEK/DEC_Arca_clamp_tightener.stl
13.4 x 13.4 x 11.7
