w4rkvs/OG-star-tracker-/v1/mechanics/top asembly/ball head holder.stl

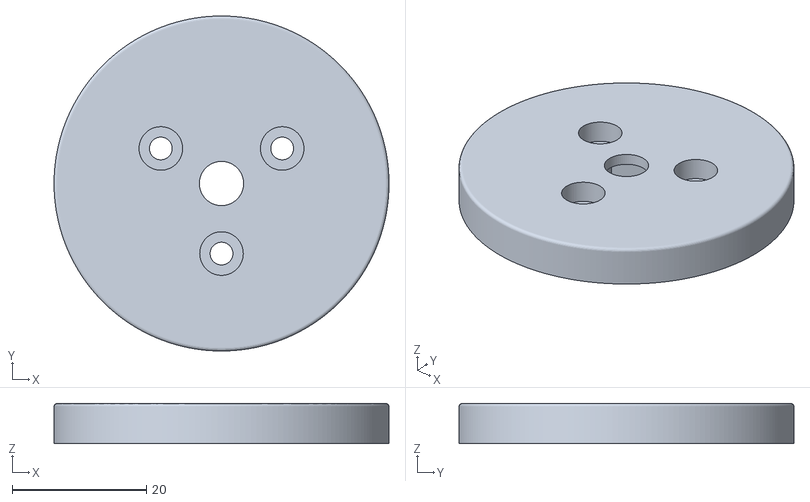
[picture p72: CAD file, 2024-11-18]
v1/mechanics/top asembly/ball head holder.stl
50.0 x 50.0 x 6.00
