w4rkvs/OG-star-tracker-/mechanics/DEC upgrade RADEK/DEC_Arca_clamp_static.stl

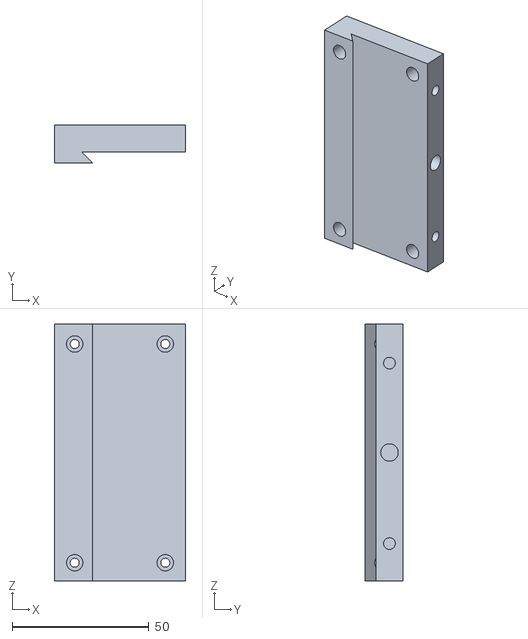
[picture p73: CAD file, 2024-11-18]
mechanics/DEC upgrade RADEK/DEC_Arca_clamp_static.stl
48.0 x 14.0 x 94.0
