w4rkvs/OG-star-tracker-/mechanics/DEC upgrade RADEK/dec-doors.stl

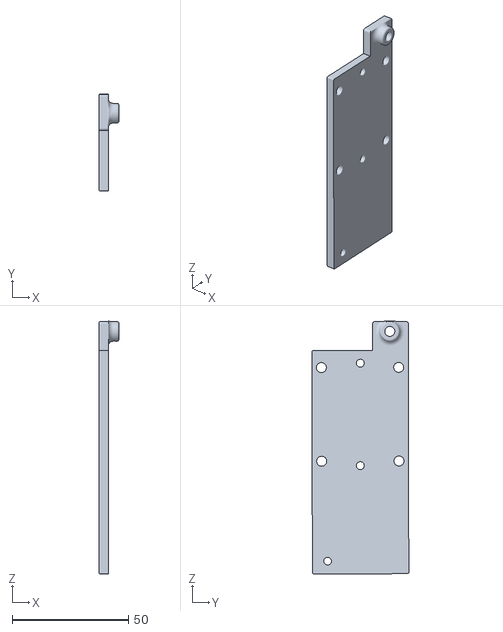
[picture p74: CAD file, 2024-11-18]
mechanics/DEC upgrade RADEK/dec-doors.stl
8.50 x 41.6 x 108.7
