w4rkvs/OG-star-tracker-/mechanics/Knobs and rest of the things/top knob m3 right.stl

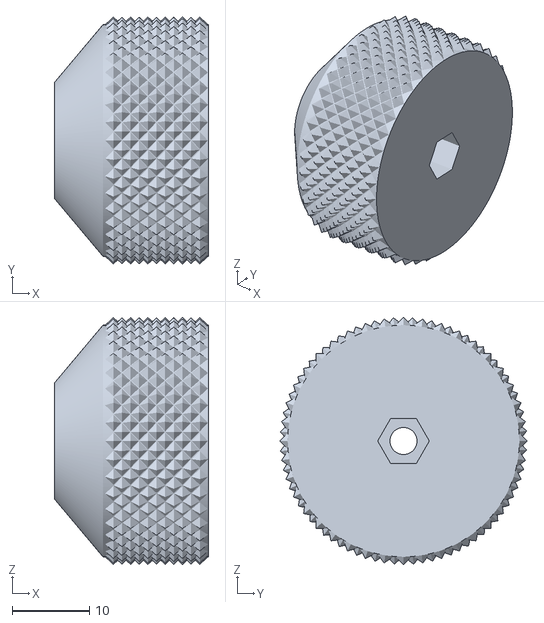
[picture p75: CAD file, 2024-11-18]
mechanics/Knobs and rest of the things/top knob m3 right.stl
20.0 x 32.0 x 32.0
