w4rkvs/OG-star-tracker-/mechanics/Top assembly/3 part of gearbox.stl

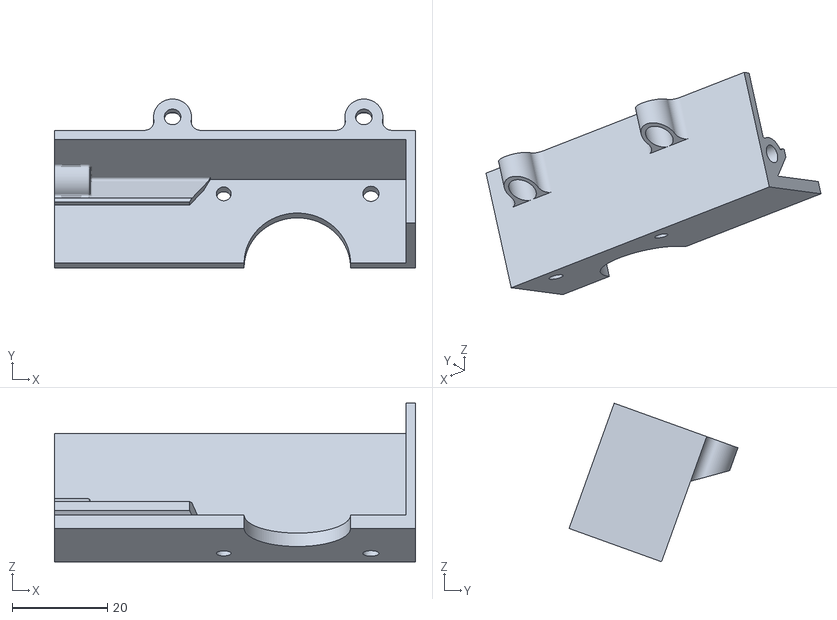
[picture p76: CAD file, 2024-11-18]
mechanics/Top assembly/3 part of gearbox.stl
76.0 x 35.6 x 33.4
