w4rkvs/OG-star-tracker-/mechanics/DEC upgrade RADEK/top-part.stl

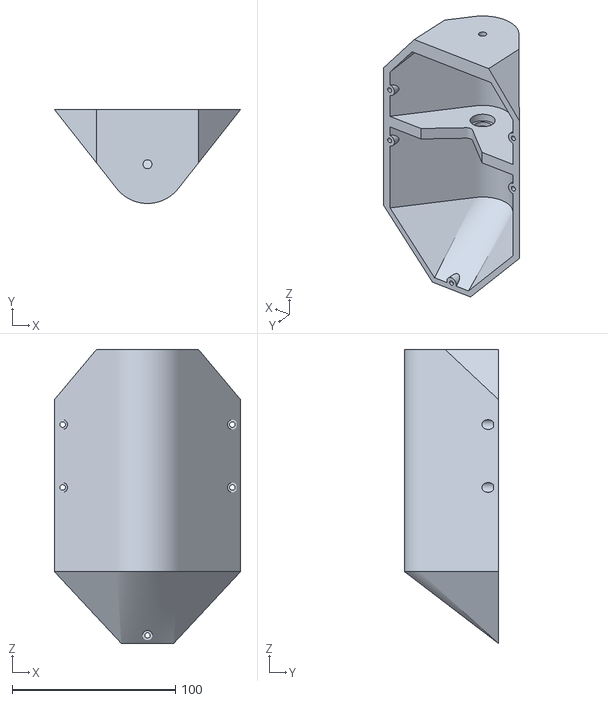
[picture p77: CAD file, 2024-11-18]
mechanics/DEC upgrade RADEK/top-part.stl
113.9 x 57.5 x 180.0
