w4rkvs/OG-star-tracker-/mechanics/Top assembly/Cover and tightener for north 60-65.stl

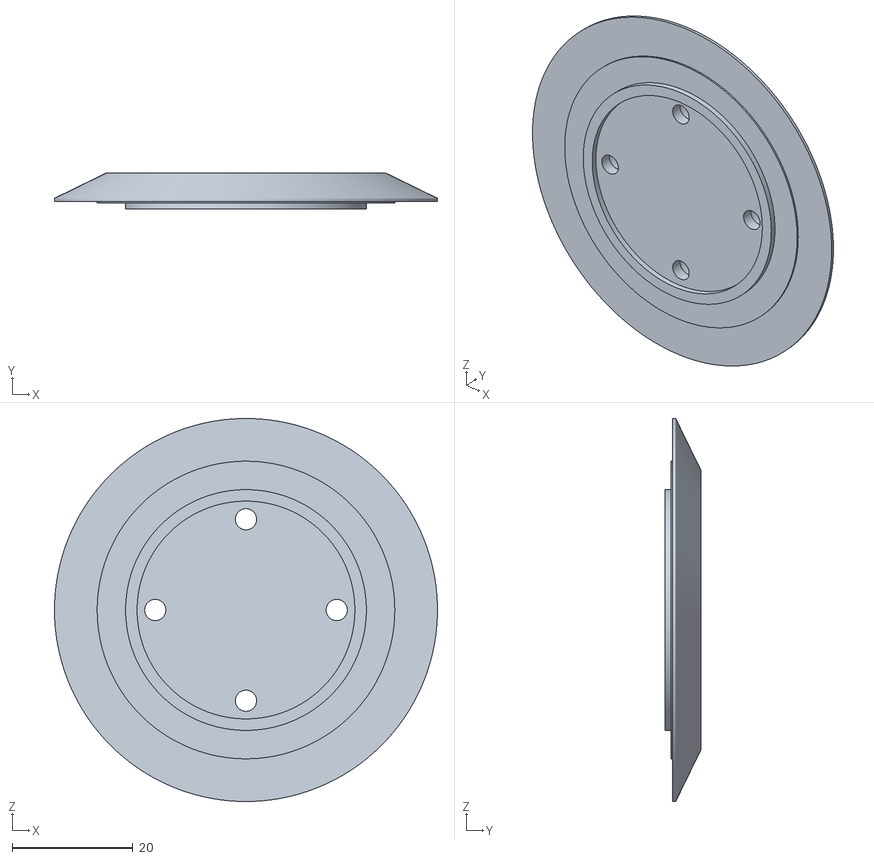
[picture p78: CAD file, 2024-11-18]
mechanics/Top assembly/Cover and tightener for north 60-65.stl
63.3 x 6.00 x 63.3
