w4rkvs/OG-star-tracker-/esp32_wireless_control/firmware/strings.cpp

// Strings.cpp
#include "strings.h"

const char* TRACKING_ON = "Tracking ON";
const char* TRACKING_OFF = "Tracking OFF";
const char* IDLE = "Idle";
const char* SPEED = "speed";
const char* TRACKING_SPEED = "trackingSpeed";
const char* DIRECTION = "direction";
const char* SLEWING = "Slewing";
const char* EXPOSURE = "exposure";
const char* NUM_EXPOSURES = "numExposures";
const char* DITHER_ENABLED = "ditherEnabled";
const char* FOCAL_LENGTH = "focalLength";
const char* DISABLE_TRACKING_ON_FINISH = "disableTracking";
const char* PIXEL_SIZE = "pixSize";
const char* CAPTURE_ON = "Capture ON";
const char* CAPTURE_OFF = "Capture OFF";
const char* CAPTURE_ALREADY_ON = "Capture Already ON";
const char* CAPTURE_ALREADY_OFF = "Capture Already OFF";
const char* CAPTURES_REMAINING = "%d Captures Remaining...";

const char* INVALID_EXPOSURE_VALUES = "Invalid Exposure Values!";
const char* INVALID_DITHER_VALUES = "Invalid Dither Settings!";

const char* MIME_TYPE_TEXT = "text/plain";
const char* MIME_TYPE_HTML = "text/html";

const char* html = 
"<DOCTYPE html> \n" 
"<html lang=\"en\"> \n" 
"<head> \n" 
" <title>OG Star Tracker Control Panel</title> \n" 
" <meta charset='utf-8'> \n" 
" <meta name='viewport' content='width=device-width, initial-scale=1.0'>\n" 
" <style> \n" 
"     body { \n" 
"         background-color: #000000; \n" 
"         text-align: center; \n" 
"         font-family: system-ui; \n" 
"         display: flex;\n" 
"         padding: 10px; \n" 
"         justify-content: center; \n" 
"     } \n" 
"     button { \n" 
"         background-color: #FF0000; \n" 
"         color: black; \n" 
"         border: none; \n" 
"         padding: 10px 10px; \n" 
"         border-radius: 40px; \n" 
"         text-align: center; \n" 
"         text-decoration: none; \n" 
"         display: inline-block; \n" 
"         font-size: 14px; \n" 
"         font-family: system-ui; \n" 
"         margin-top: 10px; \n" 
"         cursor: pointer; \n" 
"         width: 50%; \n" 
"         min-width: 120px; \n" 
"         font-weight: bold; \n" 
"     } \n" 
"     select { \n" 
"         font-size: 16px; \n" 
"         padding: 5px; \n" 
"         color: red; \n" 
"         background-color: #000000; \n" 
"         border: 2px solid #ff0000; \n" 
"         border-radius: 8px; \n" 
"         font-family: system-ui; \n" 
"     } \n" 
"     input[type='number'] { \n" 
"         font-size: 16px; \n" 
"         background-color: #000000; \n" 
"         padding: 5px; \n" 
"         font-family: system-ui; \n" 
"         border: 2px solid #ff0000; \n" 
"         color: red; \n" 
"         border-radius: 8px; \n" 
"         box-sizing: border-box; \n" 
"     } \n" 
"     label { \n" 
"         display: inline-block; \n" 
"         text-align: left; \n" 
"         margin: 10px; \n" 
"         font-size: 20px; \n" 
"     } \n" 
"     h1 { \n" 
"         font-size: 26px; \n" 
"         font-family: system-ui; \n" 
"         color: red; \n" 
"     } \n" 
"     h2 { \n" 
"         font-size: 24px; \n" 
"         font-family: system-ui; \n" 
"         color: red; \n" 
"     } \n" 
"     h3 { \n" 
"         font-size: 16px; \n" 
"         font-family: system-ui; \n" 
"         color: #FF6B00; \n" 
"     } \n" 
"     h4 { \n" 
"         font-size: 12px; \n" 
"         font-family: system-ui; \n" 
"         color: #FF6B00; \n" 
"     } \n" 
"     summary { \n" 
"         font-weight: bold; \n" 
"         font-family: system-ui; \n" 
"         font-size: 16px; \n" 
"         padding-top: 20px; \n" 
"         color: #FF6B00; \n" 
"     } \n" 
"     .content { \n" 
"         max-width: 450px; \n" 
"         width: 100%; \n" 
"         background-color: #000000; \n" 
"     } \n" 
"     .card { \n" 
"         background-color: #000000; \n" 
"         padding: 1px 16px 16px 16px; \n" 
"         border-radius: 32px; \n" 
"         margin-top: 20px; \n" 
"         box-shadow: 0em 0em 1em rgb(255 0 0 / 100%); \n" 
"     } \n" 
"     .grid2 { \n" 
"         display: flex; \n" 
"         flex-direction: row; \n" 
"         flex-wrap: wrap; \n" 
"         color: #FF6B00; \n" 
"         justify-content: center; \n" 
"         align-items: center; \n" 
"     } \n" 
"     .grid2 > h3 { \n" 
"         width: 50%; \n" 
"         min-width: 120px; \n" 
"     } \n" 
"     .grid2 > select, \n" 
"     .grid2 > input { \n" 
"         width: 50%; \n" 
"         min-width: 120px; \n" 
"         height: 40px; \n" 
"     } \n" 
"     .grid2 > .checkbox { \n" 
"         width: 50%; \n" 
"         min-width: 120px; \n" 
"         height: 20px; \n" 
"         margin: 0px; \n" 
"     } \n" 
"     .header { \n" 
"         display: flex; \n" 
"         justify-content: center; \n" 
"     } \n" 
"     #logo { \n" 
"         background-image: url('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'); \n" 
"         width: 150px; \n" 
"         height: 120px; \n" 
"         margin-top: 10px; \n" 
"     } \n" 
"     .button-group { \n" 
"         padding-top: 10px; \n" 
"         display: flex; \n" 
"         flex-wrap: wrap; \n" 
"         justify-content: center; \n" 
"     } \n" 
"     .right-separator { \n" 
"         border-right: 2px solid #000000; \n" 
"         -webkit-user-select: none; /* Safari, Chrome */ \n" 
"         -moz-user-select: none; /* Firefox */ \n" 
"         -ms-user-select: none; /* Internet Explorer/Edge */ \n" 
"         user-select: none; /* Standard property */ \n" 
"         -webkit-touch-callout: none; /* Disable callout menu on iOS */ \n" 
"     } \n" 
"     .left-separator { \n" 
"         border-left: 2px solid #000000; \n" 
"         -webkit-user-select: none; /* Safari, Chrome */ \n" 
"         -moz-user-select: none; /* Firefox */ \n" 
"         -ms-user-select: none; /* Internet Explorer/Edge */ \n" 
"         user-select: none; /* Standard property */ \n" 
"         -webkit-touch-callout: none; /* Disable callout menu on iOS */ \n" 
"     } \n" 
"     #status { \n" 
"         font-size: 24px; \n" 
"         margin: 0px; \n" 
"         font-family: system-ui; \n" 
"     } \n" 
" </style> \n" 
" <script> \n" 
"     var lastClick = 0; \n" 
"     var delay = 500; \n" 
"     function sendRequest(url) { \n" 
"         var xhr = new XMLHttpRequest(); \n" 
"         xhr.onreadystatechange = function () { \n" 
"             if (this.readyState == 4 && this.status == 200) { \n" 
"                 document.getElementById('status').innerHTML = this.responseText; \n" 
"             } \n" 
"         }; \n" 
"         xhr.open('GET', url, true); \n" 
"         xhr.send(); \n" 
"     } \n" 
"     setInterval(function () { \n" 
"         sendRequest('/status'); \n" 
"     }, 5000); \n" 
"        function requestFirmwareVersion() {\n"
"            var xhr = new XMLHttpRequest();\n"
"            xhr.onreadystatechange = function () {\n"
"                if (this.readyState == 4 && this.status == 200) {\n"
"                    document.getElementById('firmware').innerHTML = 'Firmware Version: ' + this.responseText;\n"
"                }\n"
"            };\n"
"            xhr.open('GET', '/version', true);\n"
"            xhr.send();\n"
"        }\n"
"\n"
"     function sendStartRequest(url) { \n" 
"         var direction = document.getElementById('hemisphere-select').value; \n" 
"         var trackingSpeed = document.getElementById('tracking-speed-select').value; \n" 
"         var starturl = url + '?direction=' + direction + '&trackingSpeed=' + trackingSpeed; \n" 
"         sendRequest(starturl); \n" 
"     } \n" 
"     function sendSlewStop() { \n" 
"         lastClick = Date.now(); \n" 
"         sendRequest('/stopslew'); \n" 
"     } \n" 
"     function sendSlewRequest(url) { \n" 
"         if (lastClick >= (Date.now() - delay)) \n" 
"             return; \n" 
"         lastClick = Date.now(); \n" 
"         var index = document.getElementById('slew-select').selectedIndex; \n" 
"         if (index == 6) { \n" 
"           var speed = document.getElementById('custom-speed').value; \n" 
"       } else { \n" 
"           var speed = document.getElementById('slew-select').value; \n" 
"       } \n" 
"       var slewurl = url + '?speed=' + speed; \n" 
"       sendRequest(slewurl); \n" 
"   } \n" 
"   function checkCustom() { \n" 
"     var index = document.getElementById('slew-select').selectedIndex; \n" 
"     if (index == 6) { \n" 
"         document.getElementById('custom-speed-text').style.display='block'; \n" 
"         document.getElementById('custom-speed').style.display='block'; \n" 
"     } else { \n" 
"         document.getElementById('custom-speed-text').style.display='none'; \n" 
"         document.getElementById('custom-speed').style.display='none'; \n" 
"     } \n" 
" } \n" 
" function sendCaptureRequest() { \n" 
"     var exposure = document.getElementById('exposure').value.trim(); \n" 
"     var numExposures = document.getElementById('num-exposures').value.trim(); \n" 
"     var focalLength = document.getElementById('focal_len').value.trim(); \n" 
"     var pixSize = Math.floor(parseFloat(document.getElementById('pixel_size').value.trim()) * 100); \n" 
"     var disableTracking = document.getElementById('Disable_tracking_End').checked ? 1 : 0;\n"
"     var ditherEnabled = document.getElementById('dither_on').checked ? 1 : 0; \n" 
"     var intervalometerUrl = '/start?exposure=' + exposure + '&numExposures=' + numExposures + '&focalLength=' + focalLength + '&pixSize=' + pixSize + '&ditherEnabled=' + ditherEnabled +'&disableTracking=' + disableTracking;\n"
"     sendRequest(intervalometerUrl); \n" 
" } \n" 
"</script> \n" 
"</head> \n" 
"<body onload=\"requestFirmwareVersion()\" >\n"
" <div class=\"content\"> \n" 
"     <div class=\"header\"> \n" 
"         <div id=\"logo\"></div> \n" 
"     </div> \n" 
"     <h1>TRACKER CONTROLLER</h1> \n" 
"     <div class=\"card\"> \n" 
"         <h2>Tracking</h2> \n" 
"         <div class=\"grid2\"> \n" 
"             <h3>Hemisphere:</h3> \n" 
"             <select aria-label=\"Hemisphere\" id='hemisphere-select'> \n" 
"                 <option value='1' %north%>North</option> \n" 
"                 <option value='0' %south%>South</option> \n" 
"             </select><br> \n" 
"         </div> \n" 
"         <div class=\"grid2\"> \n" 
"             <h3>Tracking Rate:</h3> \n" 
"             <select aria-label=\"tspeed\" id='tracking-speed-select'> \n" 
"                 <option value='0'>Sidereal</option> \n" 
"                 <option value='1'>Solar</option> \n" 
"                 <option value='2'>Lunar</option> \n" 
"             </select><br> \n" 
"         </div> \n" 
"         <div class=\"button-group\"> \n" 
"             <button class=\"right-separator\" type=\"button\" onclick=\"sendStartRequest('/on')\">ON</button> \n" 
"             <button class=\"left-separator\" type=\"button\" onclick=\"sendRequest('/off')\">OFF</button> \n" 
"         </div> \n" 
"     </div> \n" 
"     <div class=\"card\"> \n" 
"         <h2>Slew Control</h2> \n" 
"         <div class=\"grid2\"> \n" 
"             <h3>Speed multiplier:</h3> \n" 
"             <select aria-label=\"slew\" id='slew-select' onchange=\"checkCustom();\"> \n" 
"                 <option value='2'>2 x Tracking Rate</option> \n" 
"                 <option value='8'>8</option> \n" 
"                 <option value='50'>50</option> \n" 
"                 <option value='100'>100</option> \n" 
"                 <option value='200'>200</option> \n" 
"                 <option value='400'>400</option> \n" 
"                 <option value='custom'>custom</option> \n" 
"             </select> \n" 
"             <h3 id='custom-speed-text' style=\"display:none\";>Custom Speed:</h3> \n" 
"             <input id='custom-speed' type='number' value='2' min='2' max='400' style=\"display:none\";/> \n" 
"             <br> \n" 
"         </div> \n" 
"         <h4>Hold direction button to slew</h4> \n" 
"         <div class=\"button-group\"> \n" 
"             <button class=\"right-separator\" type=\"button\" ontouchstart=\"sendSlewRequest('/left')\" onmousedown=\"sendSlewRequest('/left')\" ontouchend=\"sendSlewStop()\" onmouseup=\"sendSlewStop()\" onmouseleave=\"sendSlewStop()\" ontouchcancel=\"sendSlewStop()\">SLEW LEFT</button> \n" 
"             <button class=\"left-separator\" type=\"button\" ontouchstart=\"sendSlewRequest('/right')\" onmousedown=\"sendSlewRequest('/right')\" ontouchend=\"sendSlewStop()\" onmouseup=\"sendSlewStop()\" onmouseleave=\"sendSlewStop()\" ontouchcancel=\"sendSlewStop()\">SLEW RIGHT</button> \n" 
"         </div> \n" 
"         <button type=\"button\" onclick=\"sendSlewStop()\" >ABORT SLEW</button> \n" 
"     </div> \n" 
"     <div class=\"card\"> \n" 
"         <h2>Photo Control</h2> \n" 
"         <div class=\"grid2\"> \n" 
"             <h3>Exposure lenght:</h3> \n" 
"             <input type='number' id='exposure' placeholder='in seconds (Ex. 30)'> \n" 
"         </div> \n" 
"         <div class=\"grid2\"> \n" 
"             <h3>Number exposures:</h3> \n" 
"             <input type='number' id='num-exposures' placeholder='nº of photos (Ex. 20)'> \n" 
"         </div> \n" 
"            <div class=\"grid2\">\n"
"                <h3>Disable tracking on end:</h3>\n"
"                <input class=\"checkbox\" aria-label=\"Disable_Tracking_End\" type=\"checkbox\" id=\"Disable_tracking_End\" %tracking%>\n"
"            </div>\n"
"         <details> \n" 
"             <summary>Dither Settings</summary> \n" 
"             <-- Content inside the collapsible section --> \n" 
"             <div class=\"grid2\"> \n" 
"                 <h3>Dithering Enable:</h3> \n" 
"                 <input class=\"checkbox\" aria-label=\"Dithering\" type=\"checkbox\" id=\"dither_on\" %dither%> \n" 
"             </div> \n" 
"             <div class=\"grid2\"> \n" 
"                 <h3>Lens focal lenght:</h3> \n" 
"                 <input type=\"number\" id=\"focal_len\" placeholder='in milimiters (Ex. 135)' value='%focallen%'> \n" 
"             </div> \n" 
"             <div class=\"grid2\"> \n" 
"                 <h3>Camera pixel size:</h3> \n" 
"                 <input type=\"number\" id=\"pixel_size\" placeholder='in micrometer (Ex. 4.1)' value='%pixsize%' step=\"0.01\"> \n" 
"             </div> \n" 
"         </details> \n" 
"         <div class=\"button-group\"> \n" 
"             <button class=\"right-separator\" type=\"button\" onclick=\"sendCaptureRequest()\">START CAPTURE</button> \n" 
"             <button class=\"left-separator\" type=\"button\" onclick=\"sendRequest('/abort')\">ABORT CAPTURE</button> \n" 
"         </div> \n" 
"     </div> \n" 
"     <div class=\"card\"> \n" 
"         <h2>Status</h2> \n" 
"         <h3>Test Message</h3> \n" 
"  </div> \n" 
"  <h4 id='firmware'>Firmware Version: </h4>\n"
"</div> \n" 
"</body> \n" 
"</html>\n" 
 ;
