w4rkvs/OG-star-tracker-/esp32_wireless_control/firmware/strings.h

// strings.h
#ifndef STRINGS_H
#define STRINGS_H

extern const char* TRACKING_ON;
extern const char* TRACKING_OFF;
extern const char* IDLE;
extern const char* TRACKING_SPEED;
extern const char* SPEED;
extern const char* DIRECTION;
extern const char* SLEWING;
extern const char* EXPOSURE;
extern const char* NUM_EXPOSURES;
extern const char* DITHER_ENABLED;
extern const char* FOCAL_LENGTH;
extern const char* PIXEL_SIZE;
extern const char* DISABLE_TRACKING_ON_FINISH;
extern const char* CAPTURE_ON;
extern const char* CAPTURE_OFF;
extern const char* CAPTURE_ALREADY_ON;
extern const char* CAPTURE_ALREADY_OFF;
extern const char* CAPTURES_REMAINING;

extern const char* INVALID_EXPOSURE_VALUES;
extern const char* INVALID_DITHER_VALUES;

extern const char* MIME_TYPE_TEXT;
extern const char* MIME_TYPE_HTML;


extern const char* html;

#endif  // STRINGS_H
